positron48/robot/ai-renders/00023-1572373519.png

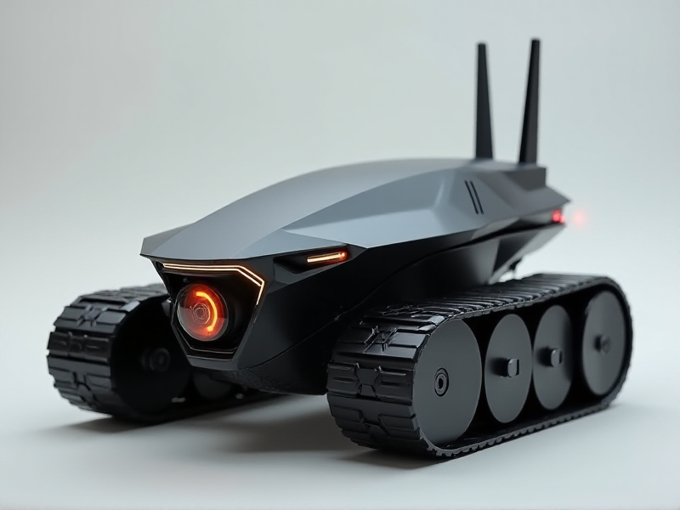
ai-renders/00023-1572373519.png
