positron48/robot/ai-renders/00040-1572373536.png

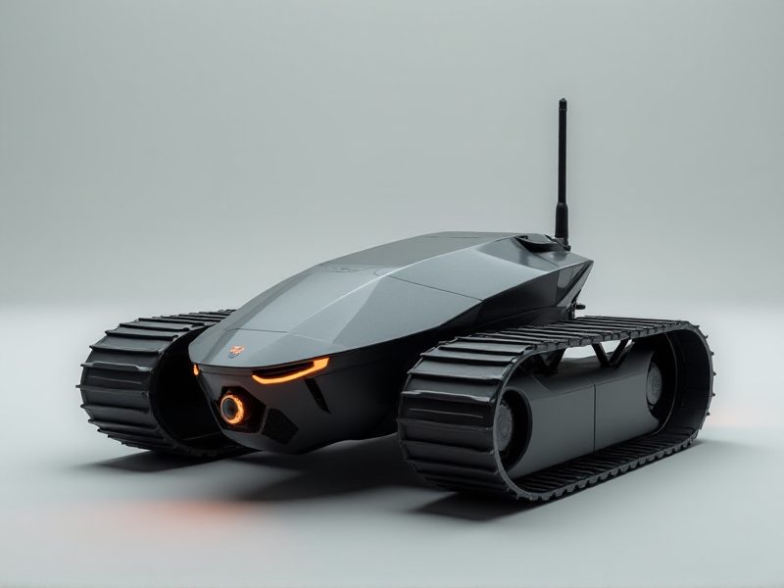
ai-renders/00040-1572373536.png
