positron48/robot/ai-renders/00042-1572373538.png

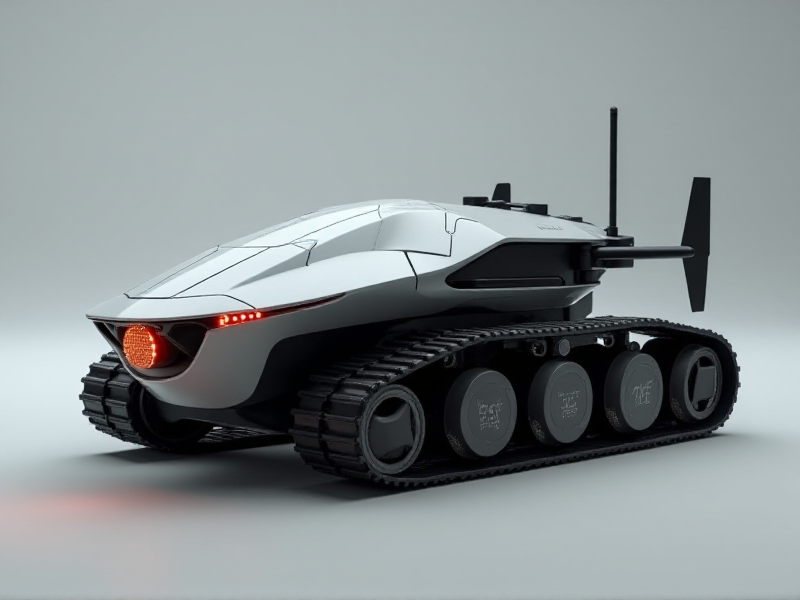
ai-renders/00042-1572373538.png
