positron48/robot/ai-renders/00055-1572373551.png

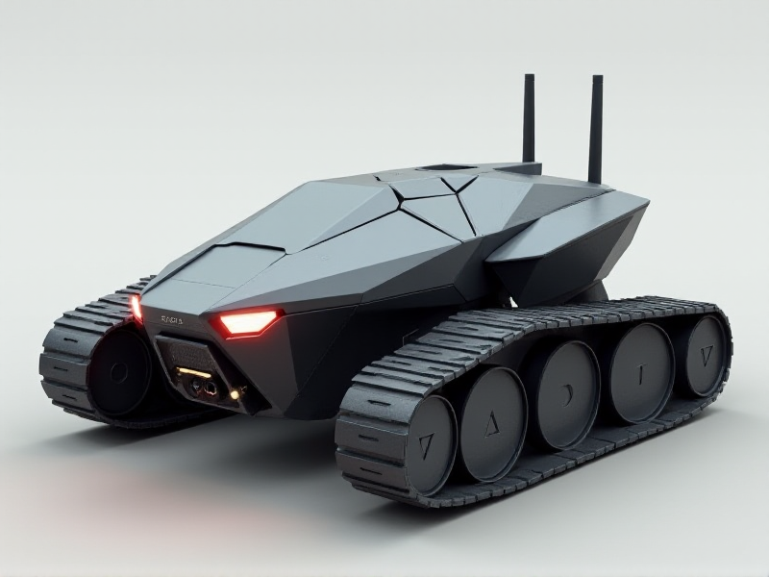
ai-renders/00055-1572373551.png
