positron48/robot/ai-renders/00080-1572373576.png

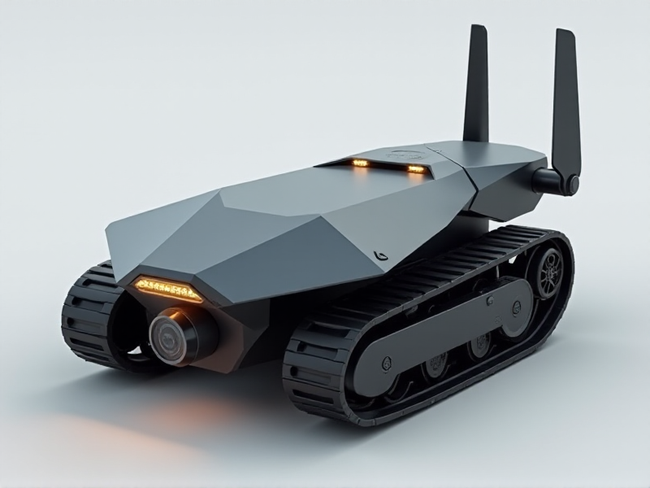
ai-renders/00080-1572373576.png
