positron48/robot/ai-renders/00095-1572373591.png

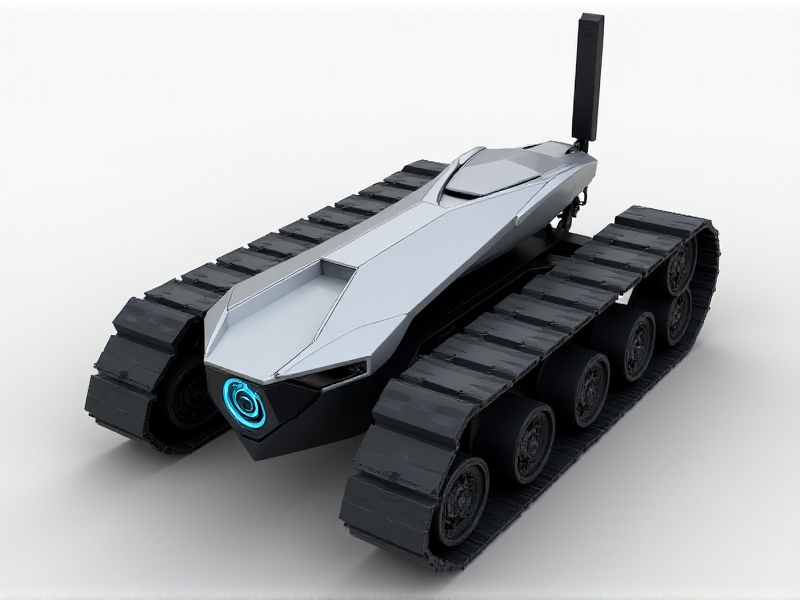
ai-renders/00095-1572373591.png
