positron48/robot/ai-renders/00117-2419401898.png

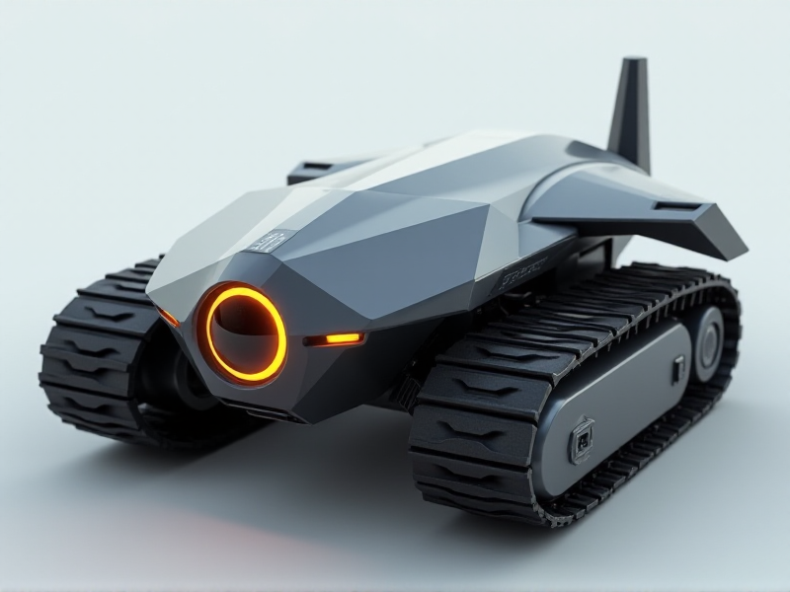
ai-renders/00117-2419401898.png
