positron48/robot/ai-renders/00122-3091978869.png

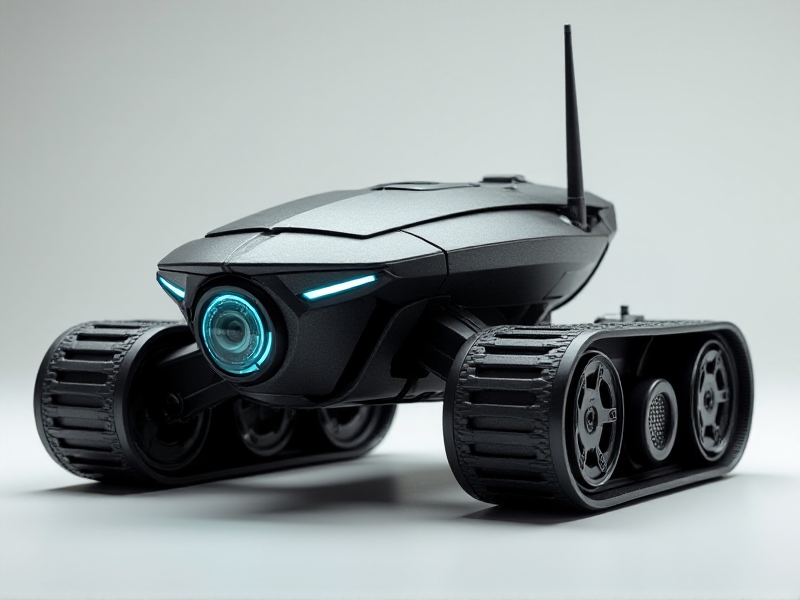
ai-renders/00122-3091978869.png
