positron48/robot/ai-renders/00186-2854738076.png

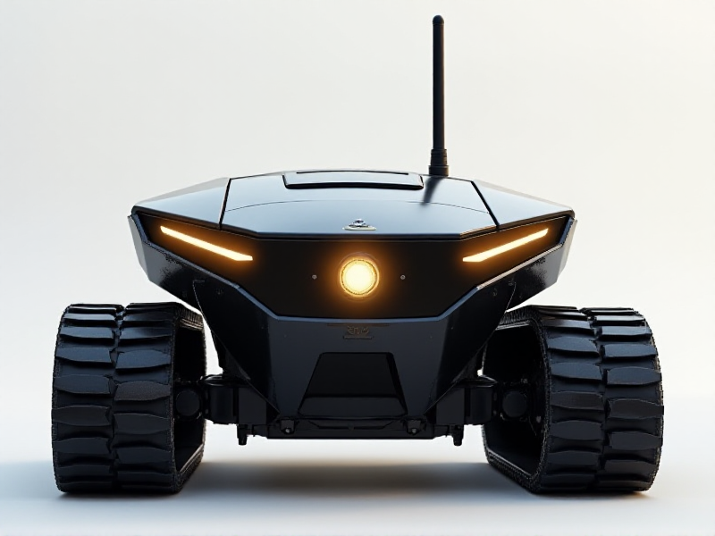
ai-renders/00186-2854738076.png
