positron48/robot/ai-renders/00576-1258968118.png

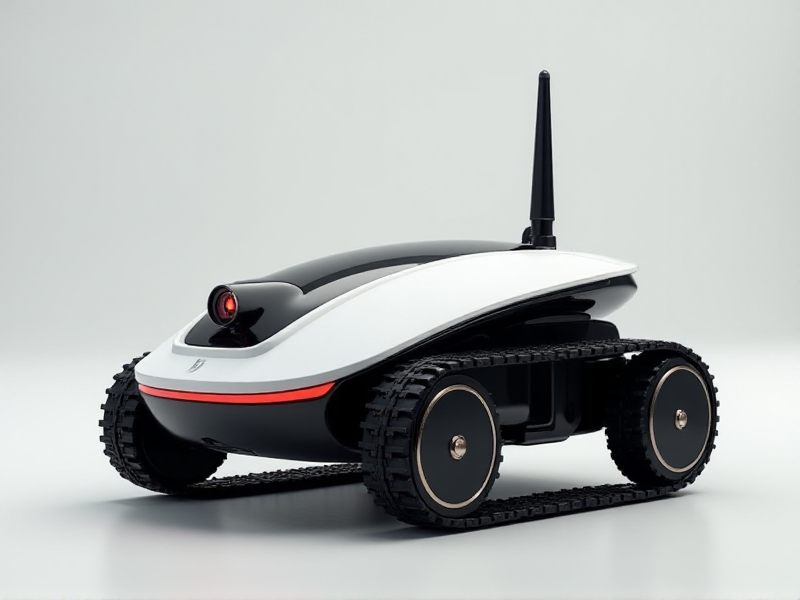
ai-renders/00576-1258968118.png
