positron48/robot/ai-renders/all/00000-357559412.png

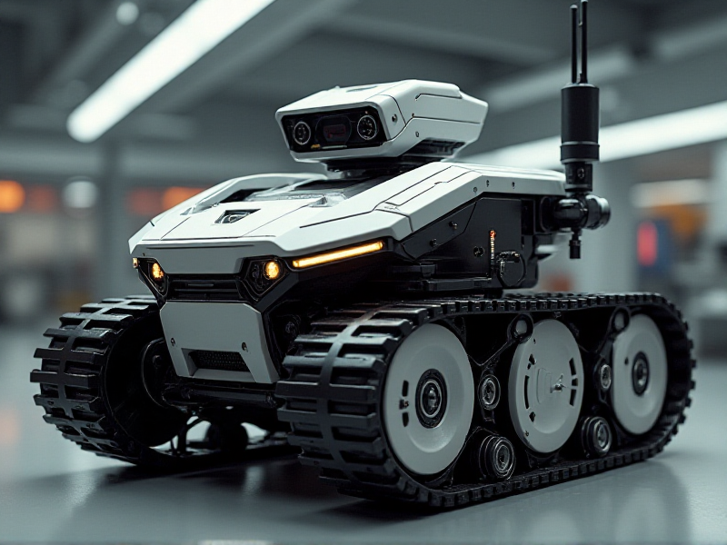
ai-renders/all/00000-357559412.png
