positron48/robot/ai-renders/all/00005-1248517951.png

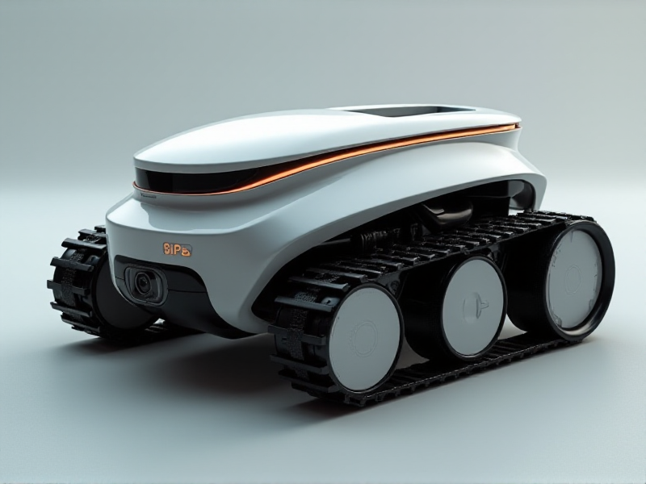
ai-renders/all/00005-1248517951.png
