positron48/robot/ai-renders/all/00009-1846332725.png

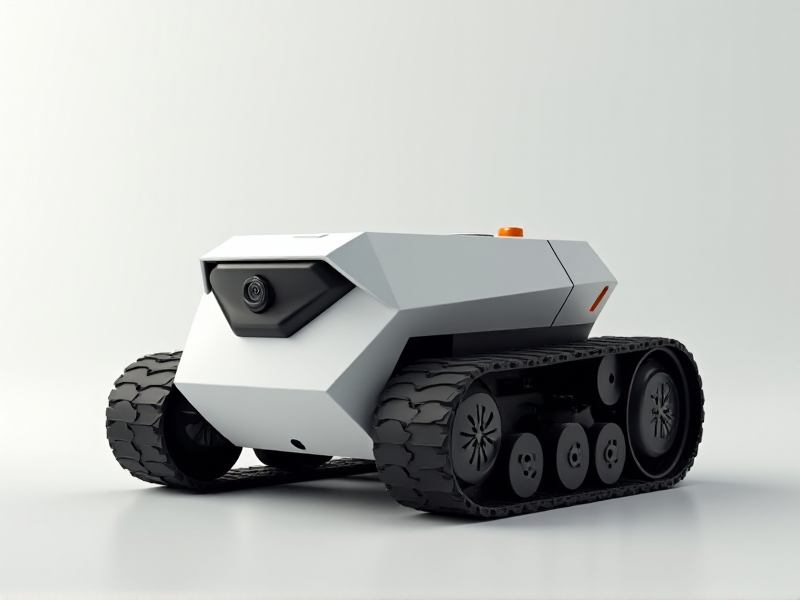
ai-renders/all/00009-1846332725.png
