positron48/robot/ai-renders/all/00010-3830520620.png

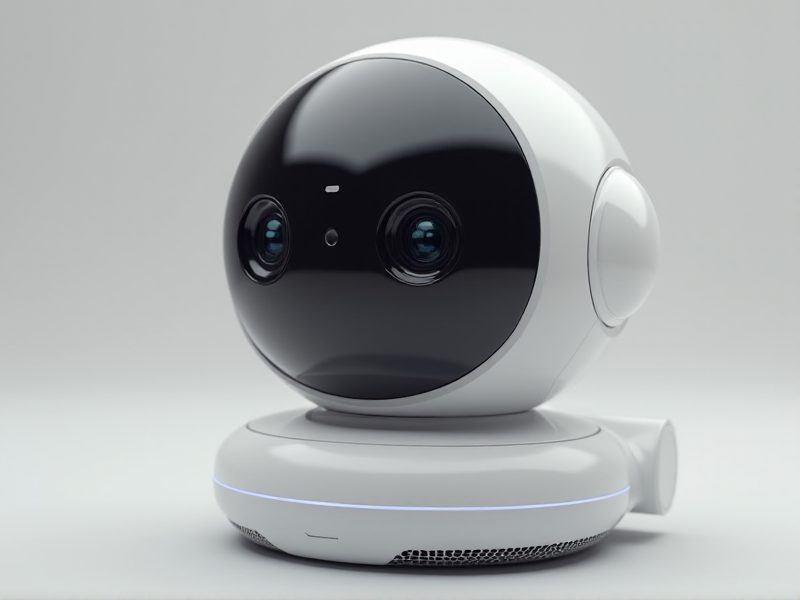
ai-renders/all/00010-3830520620.png
