positron48/robot/ai-renders/all/00015-1510084404.png

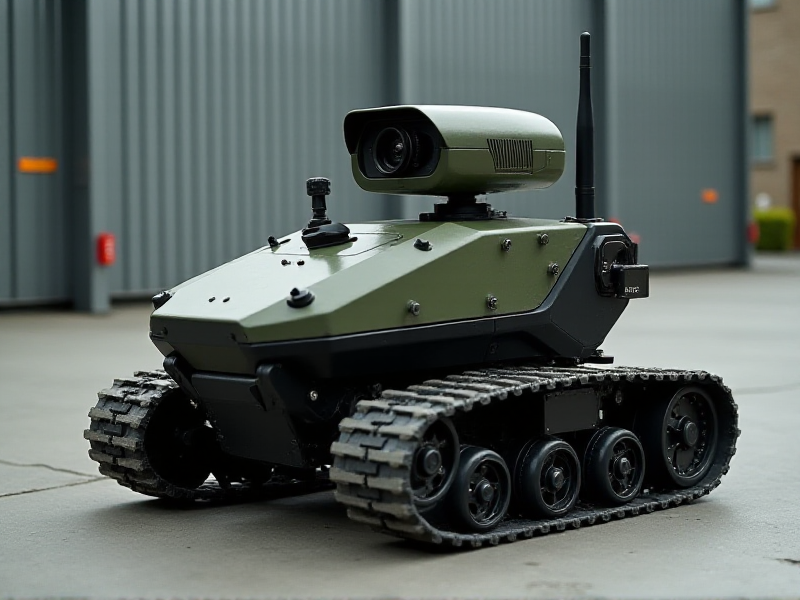
ai-renders/all/00015-1510084404.png
