positron48/robot/ai-renders/all/00020-1703099426.png

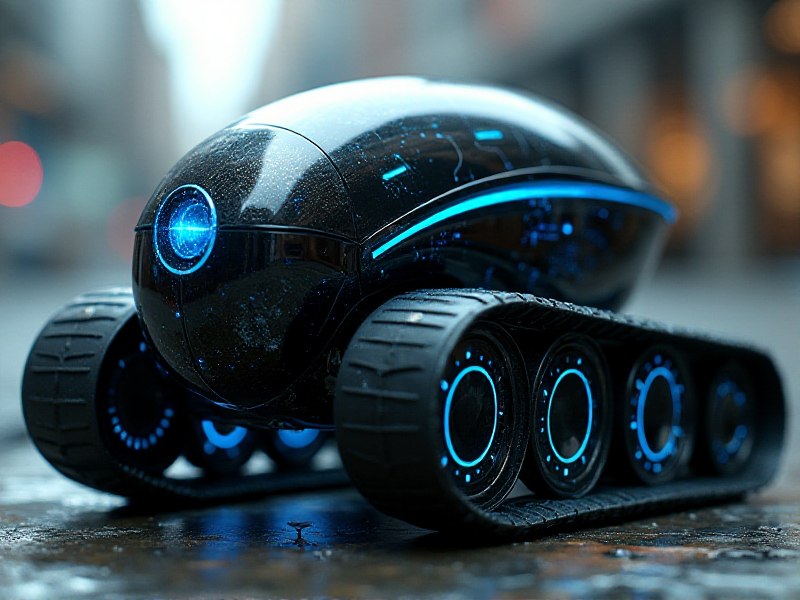
ai-renders/all/00020-1703099426.png
