positron48/robot/ai-renders/all/00024-1435315715.png

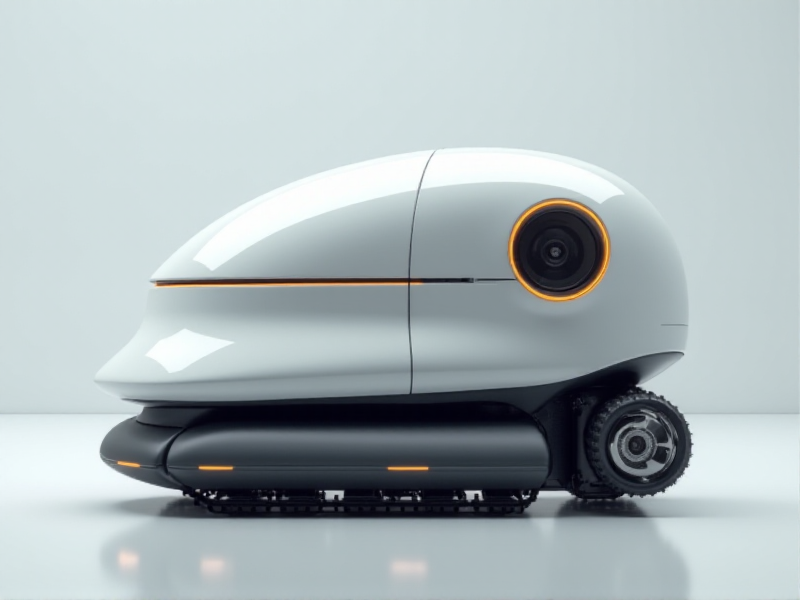
ai-renders/all/00024-1435315715.png
