positron48/robot/ai-renders/all/00025-1704890410.png

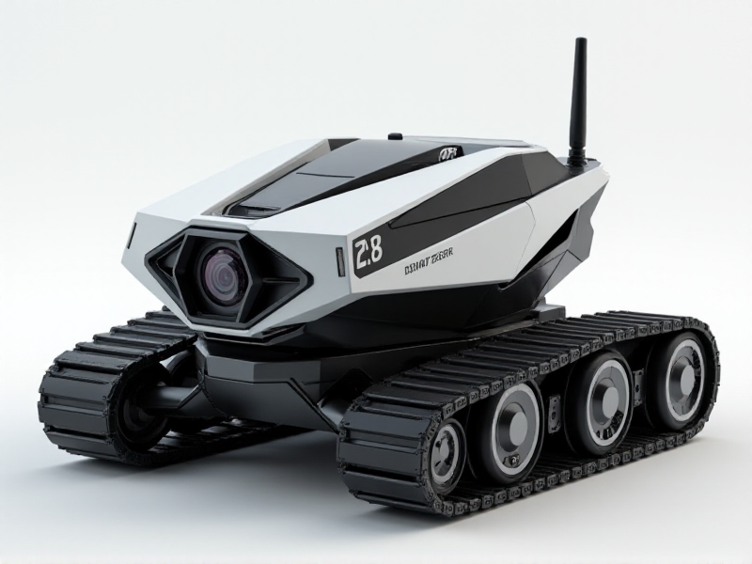
ai-renders/all/00025-1704890410.png
