positron48/robot/ai-renders/all/00030-3104922929.png

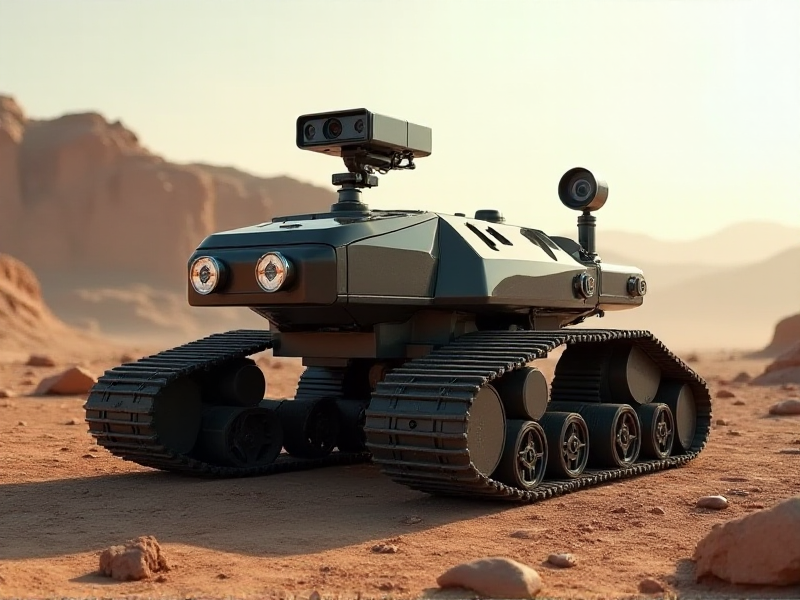
ai-renders/all/00030-3104922929.png
