positron48/robot/ai-renders/all/00035-3908900121.png

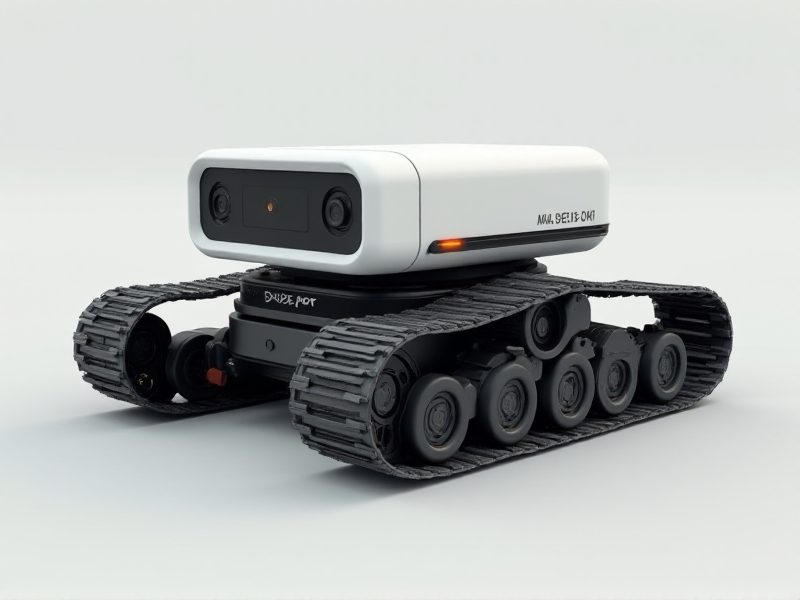
ai-renders/all/00035-3908900121.png
