positron48/robot/ai-renders/all/00039-2805063001.png

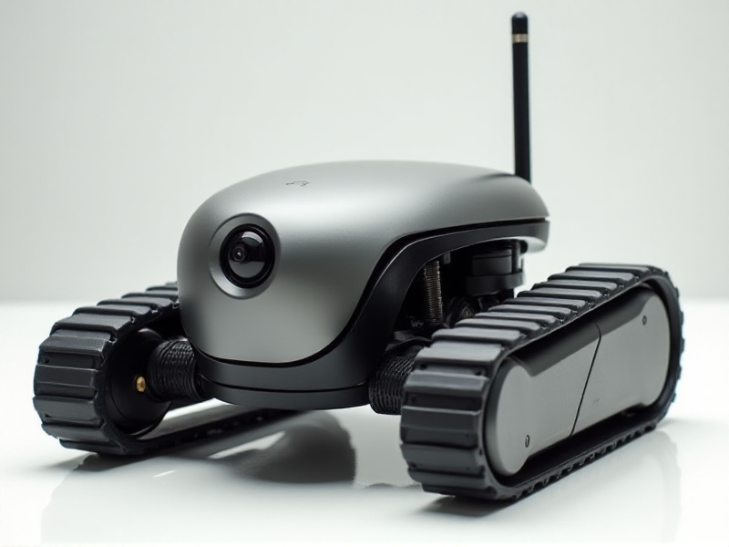
ai-renders/all/00039-2805063001.png
