positron48/robot/ai-renders/all/00040-1279062750.png

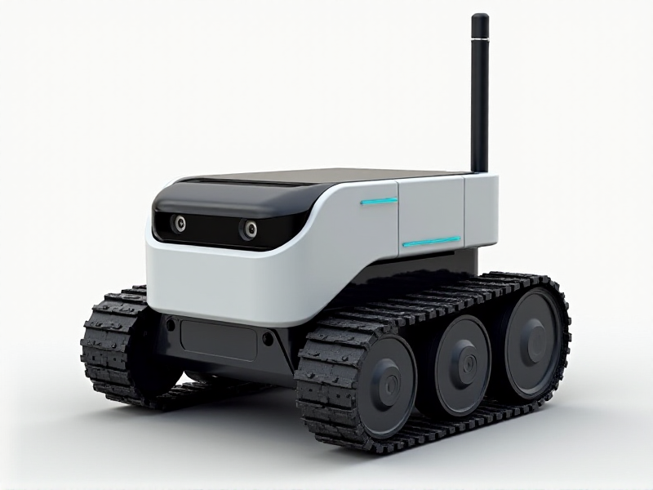
ai-renders/all/00040-1279062750.png
