positron48/robot/ai-renders/all/00045-1480606769.png

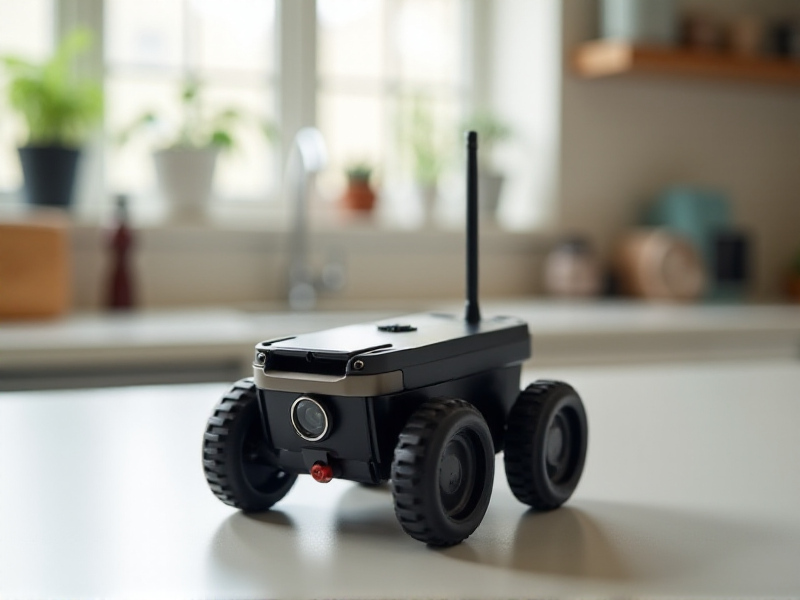
ai-renders/all/00045-1480606769.png
