positron48/robot/ai-renders/all/00050-4032314944.png

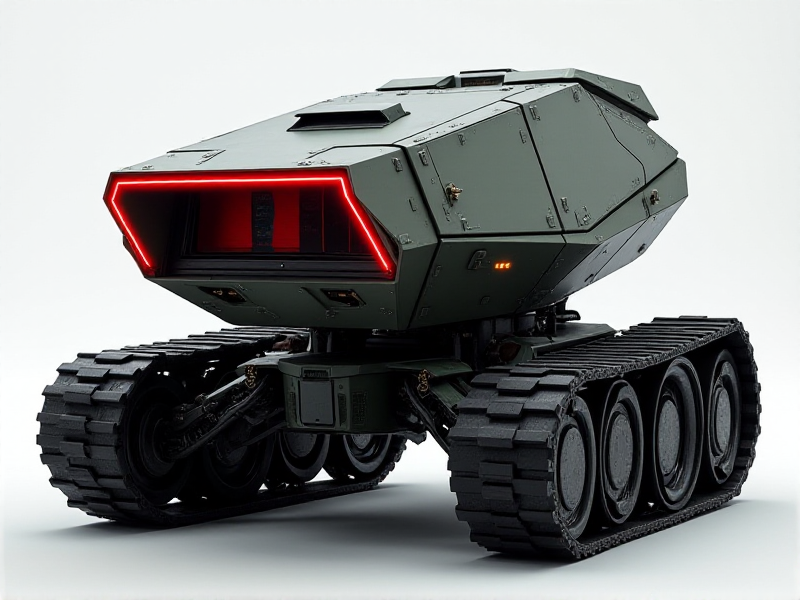
ai-renders/all/00050-4032314944.png
