positron48/robot/ai-renders/all/00054-1610239201.png

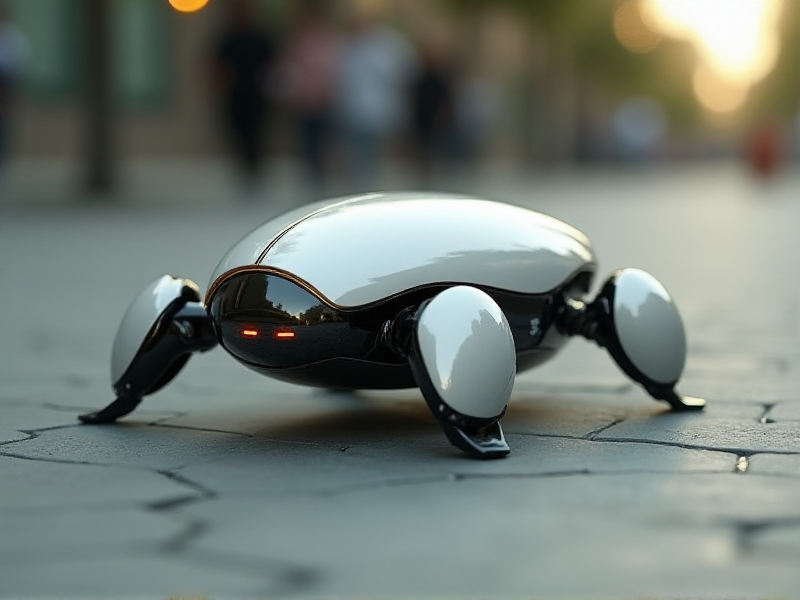
ai-renders/all/00054-1610239201.png
