positron48/robot/ai-renders/all/00055-1120741218.png

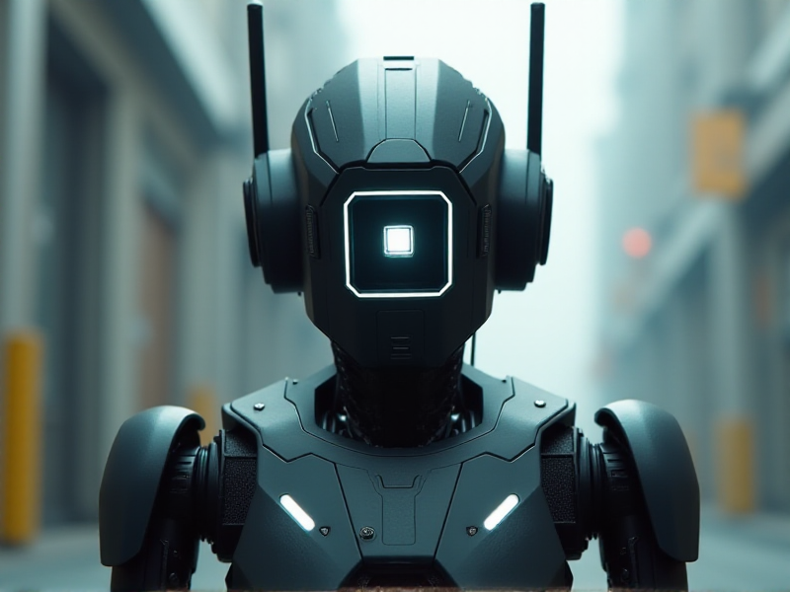
ai-renders/all/00055-1120741218.png
