positron48/robot/ai-renders/all/00060-2551709868.png

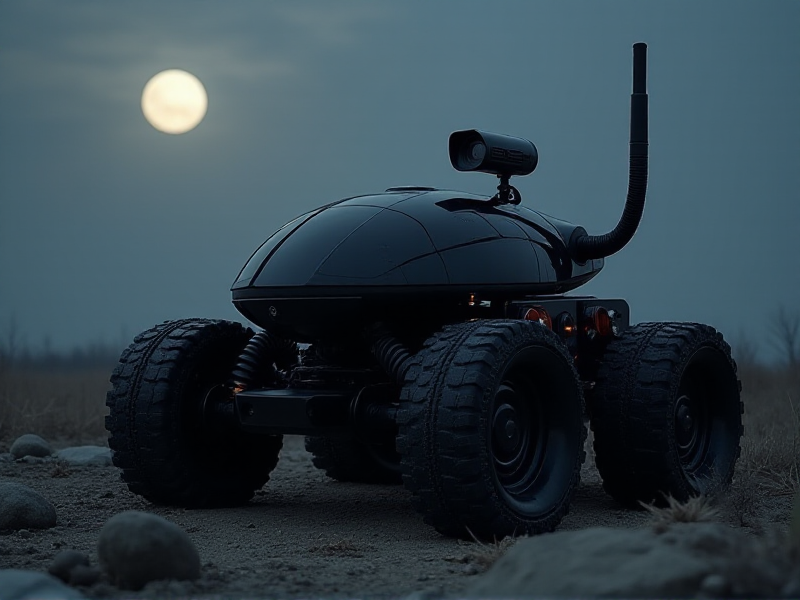
ai-renders/all/00060-2551709868.png
