positron48/robot/ai-renders/all/00065-3160654962.png

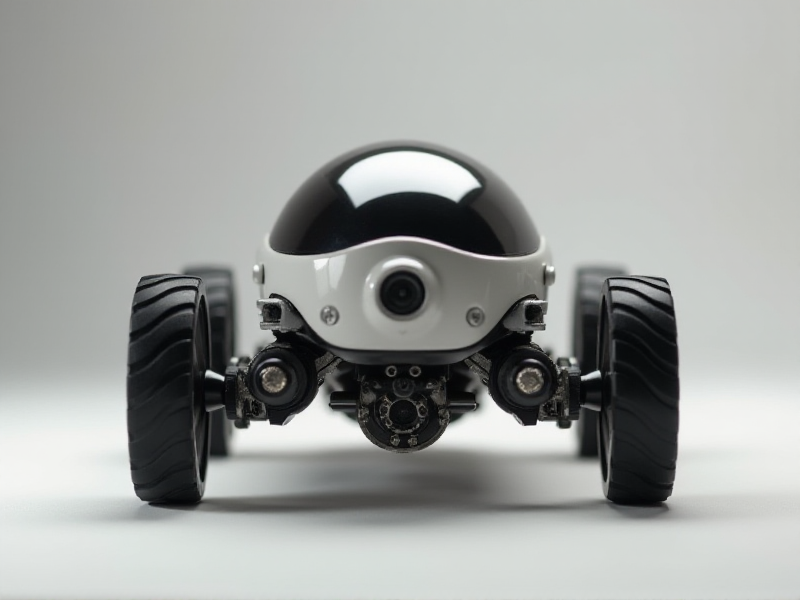
ai-renders/all/00065-3160654962.png
