positron48/robot/ai-renders/all/00069-1434522783.png

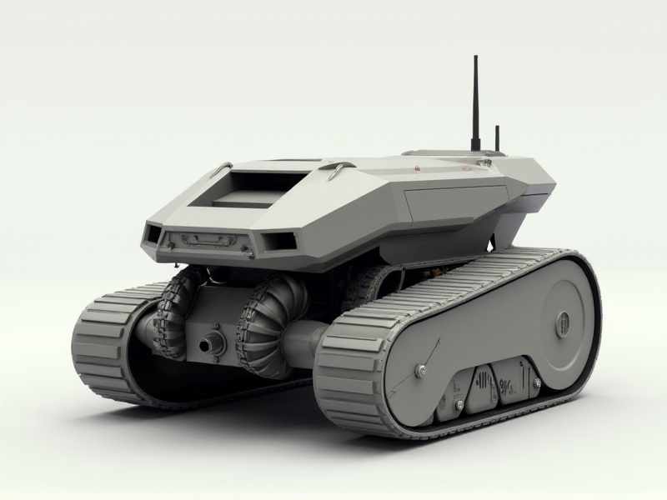
ai-renders/all/00069-1434522783.png
