positron48/robot/ai-renders/all/00070-909880307.png

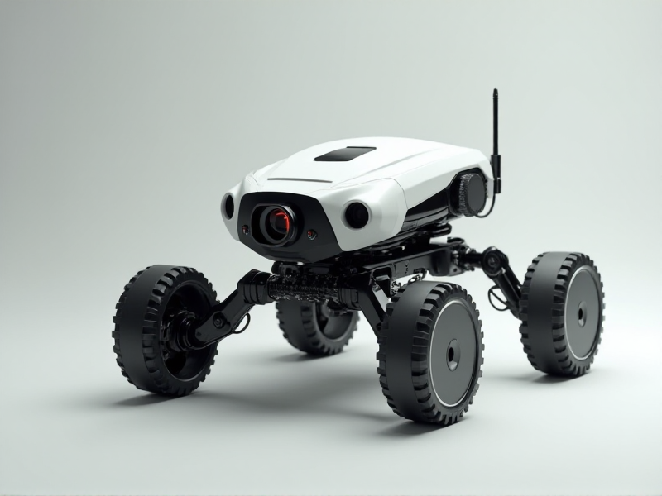
ai-renders/all/00070-909880307.png
