positron48/robot/ai-renders/all/00075-4185142455.png

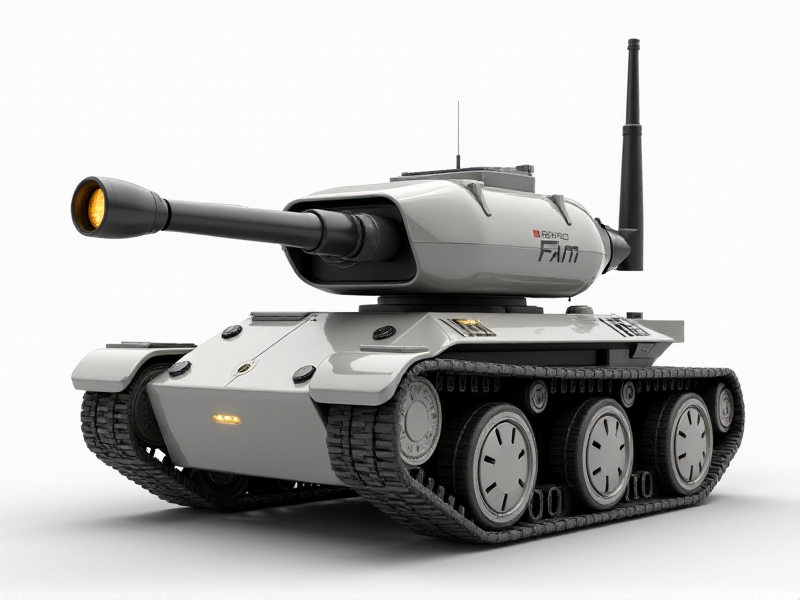
ai-renders/all/00075-4185142455.png
