positron48/robot/ai-renders/all/00080-3249783718.png

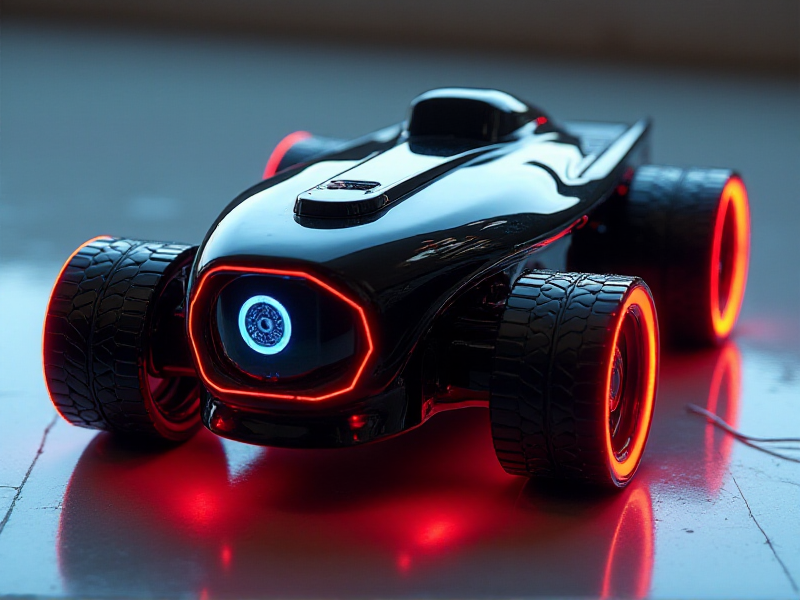
ai-renders/all/00080-3249783718.png
