positron48/robot/ai-renders/all/00085-1067350489.png

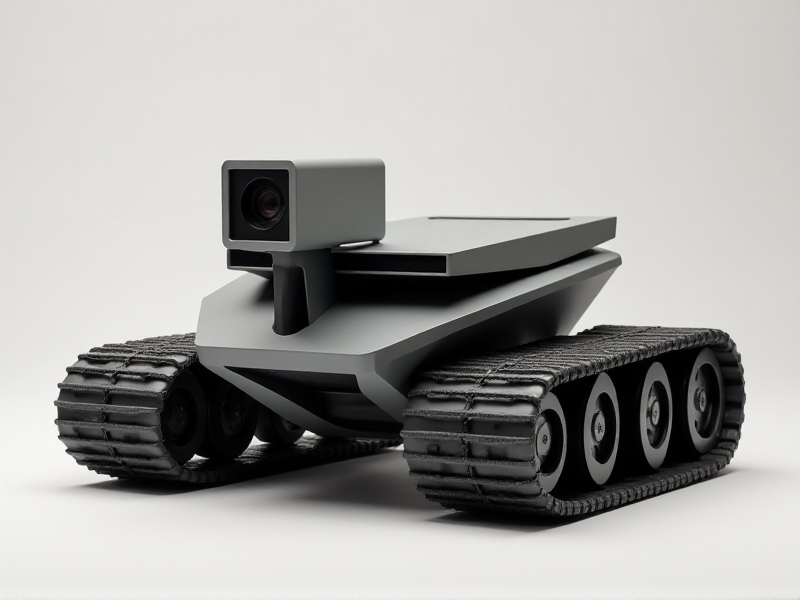
ai-renders/all/00085-1067350489.png
