positron48/robot/ai-renders/all/00090-1672998109.png

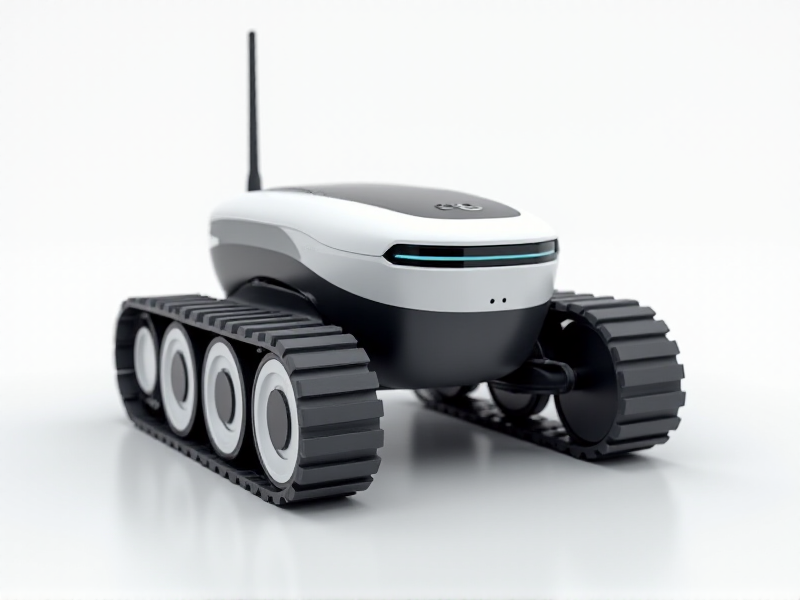
ai-renders/all/00090-1672998109.png
