positron48/robot/ai-renders/all/00095-99025422.png

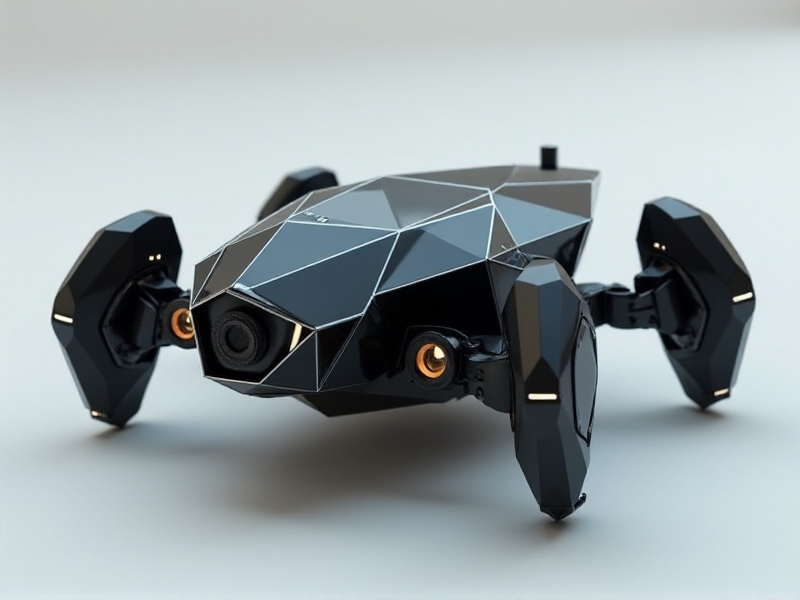
ai-renders/all/00095-99025422.png
