positron48/robot/ai-renders/all/00100-3047387080.png

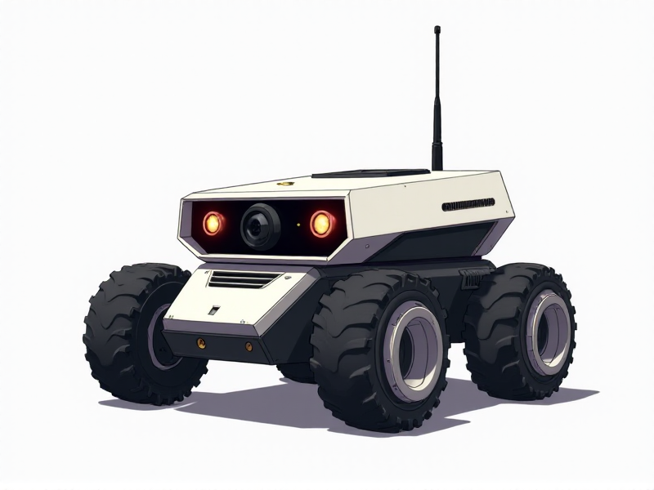
ai-renders/all/00100-3047387080.png
