positron48/robot/ai-renders/all/00105-2527510471.png

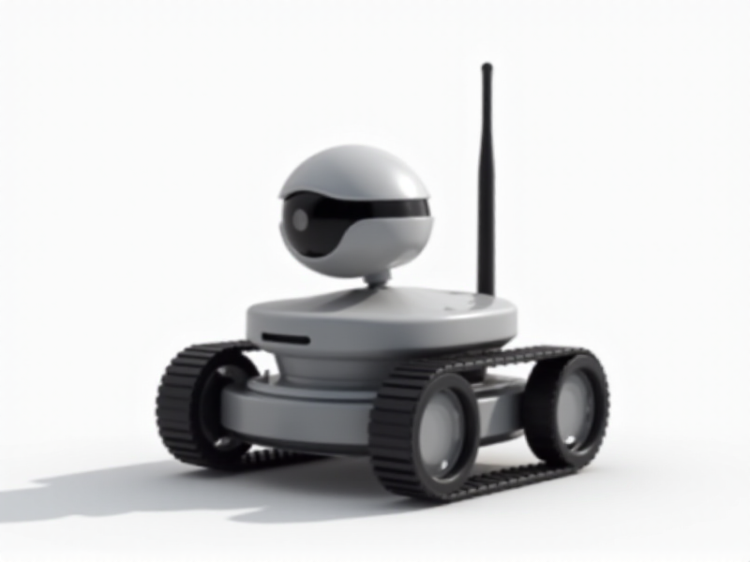
ai-renders/all/00105-2527510471.png
