positron48/robot/ai-renders/all/00110-1504034849.png

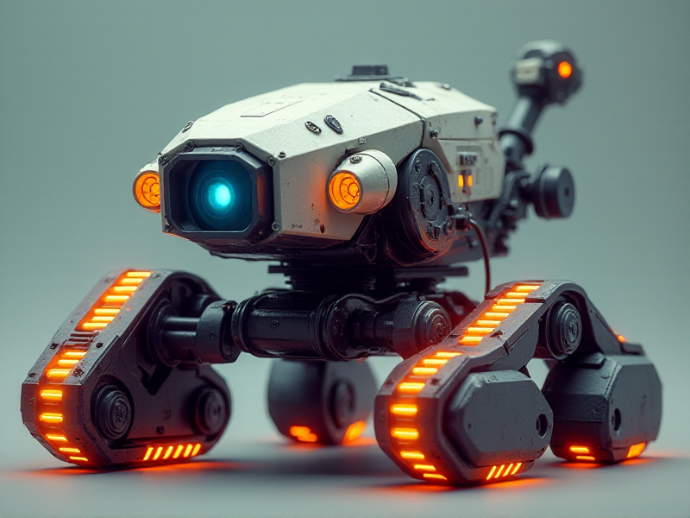
ai-renders/all/00110-1504034849.png
