positron48/robot/ai-renders/all/00115-2866515047.png

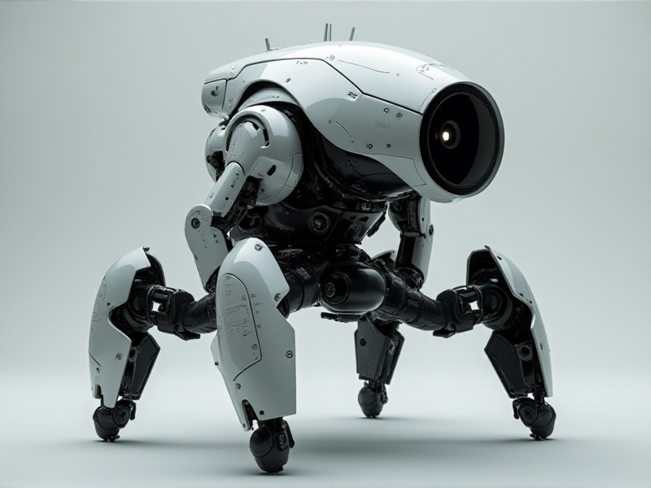
ai-renders/all/00115-2866515047.png
