positron48/robot/ai-renders/all/00120-1237886460.png

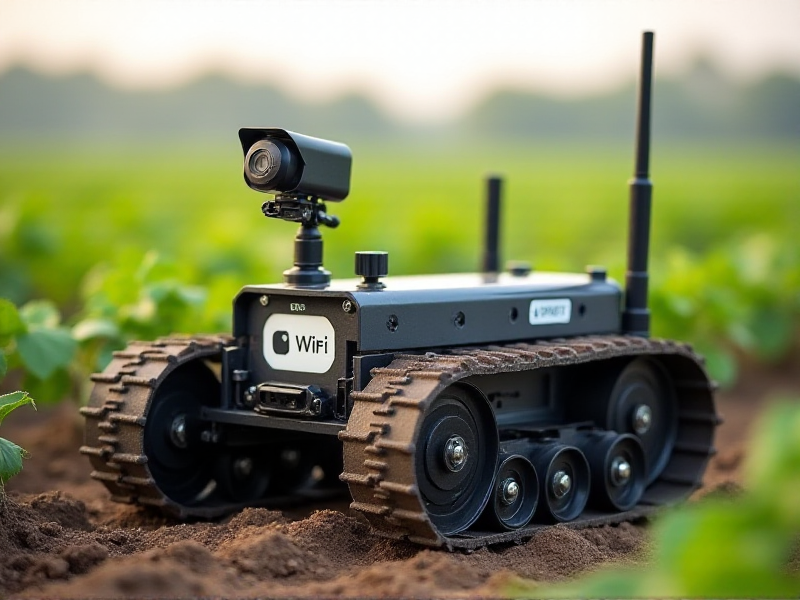
ai-renders/all/00120-1237886460.png
