positron48/robot/ai-renders/all/00125-3579262042.png

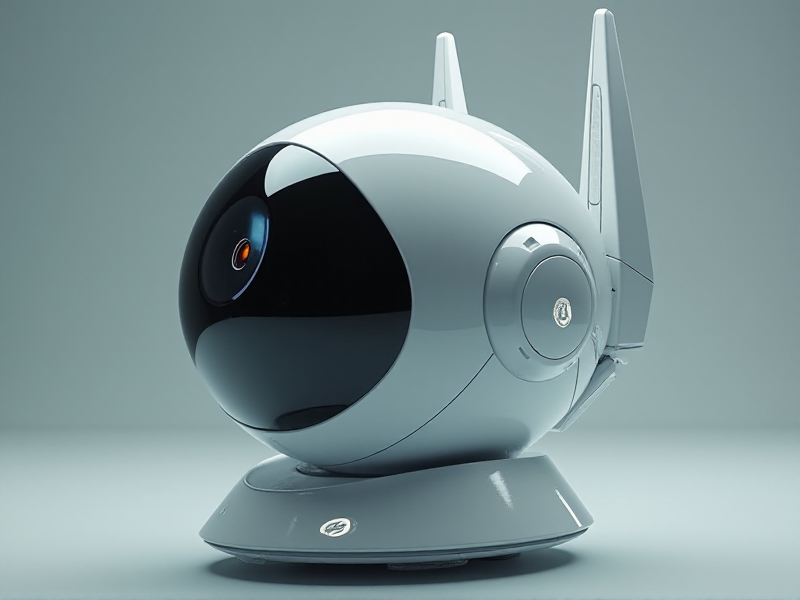
ai-renders/all/00125-3579262042.png
