positron48/robot/ai-renders/all/00130-2607103277.png

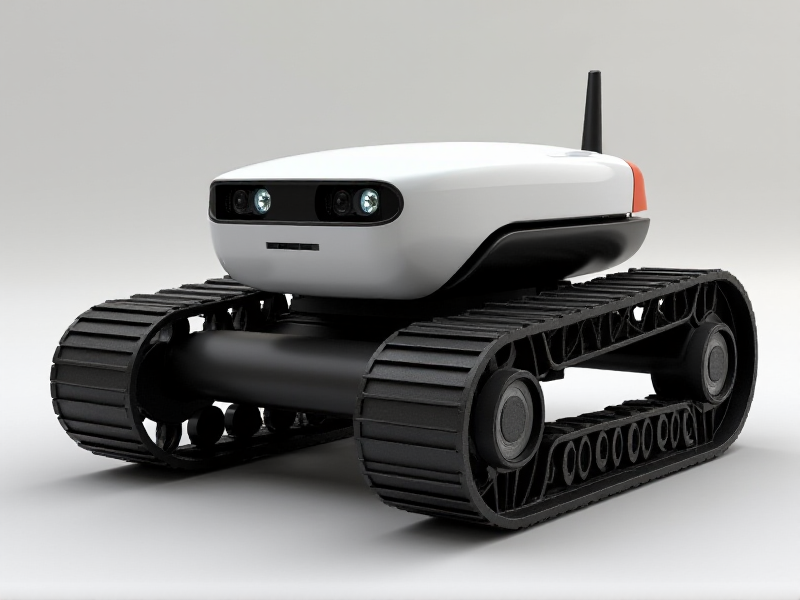
ai-renders/all/00130-2607103277.png
