positron48/robot/ai-renders/all/00135-3617314966.png

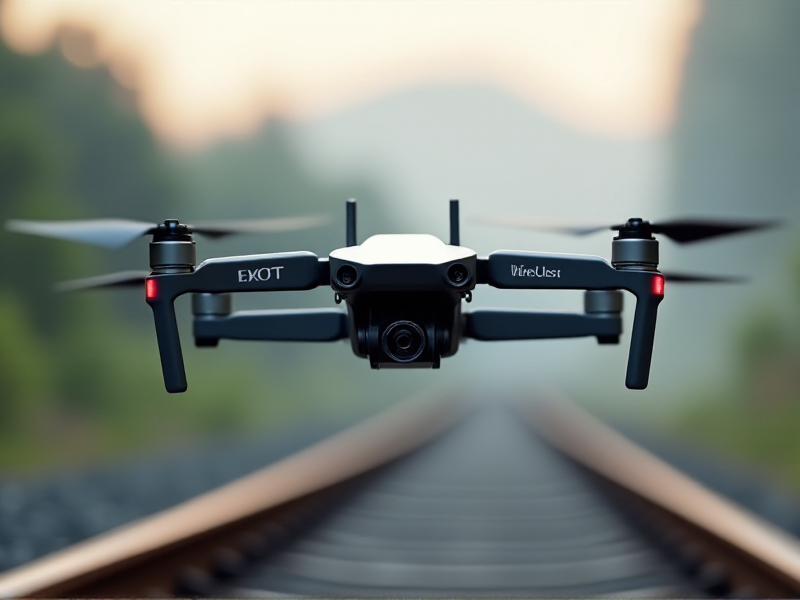
ai-renders/all/00135-3617314966.png
