positron48/robot/ai-renders/all/00140-2341996741.png

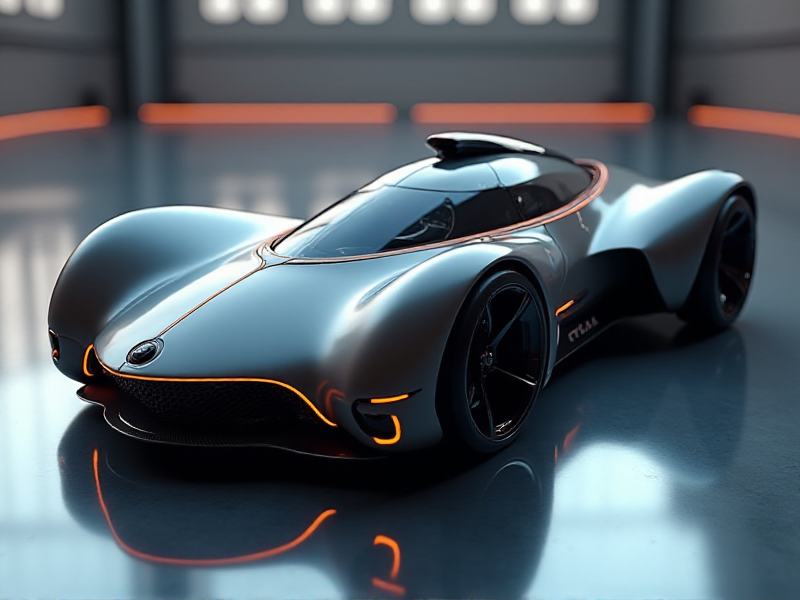
ai-renders/all/00140-2341996741.png
