positron48/robot/ai-renders/all/00145-1462839352.png

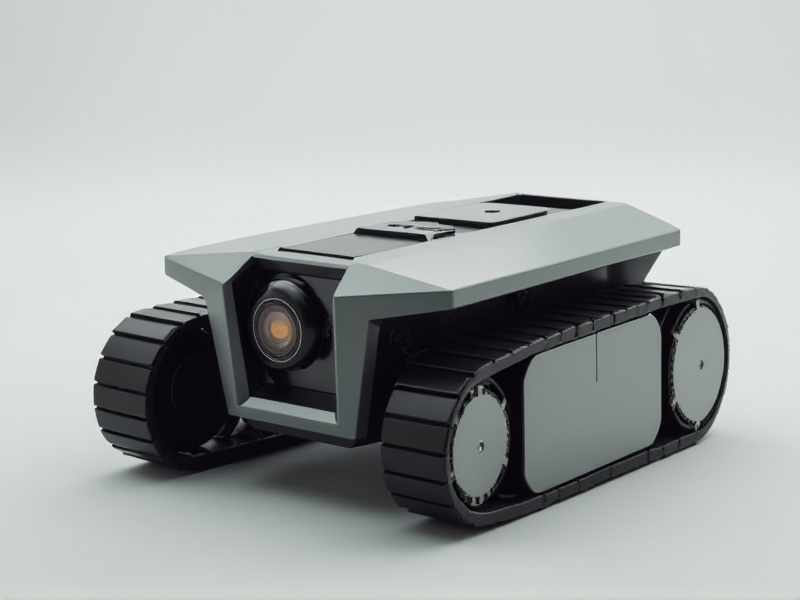
ai-renders/all/00145-1462839352.png
