positron48/robot/ai-renders/all/00150-565781888.png

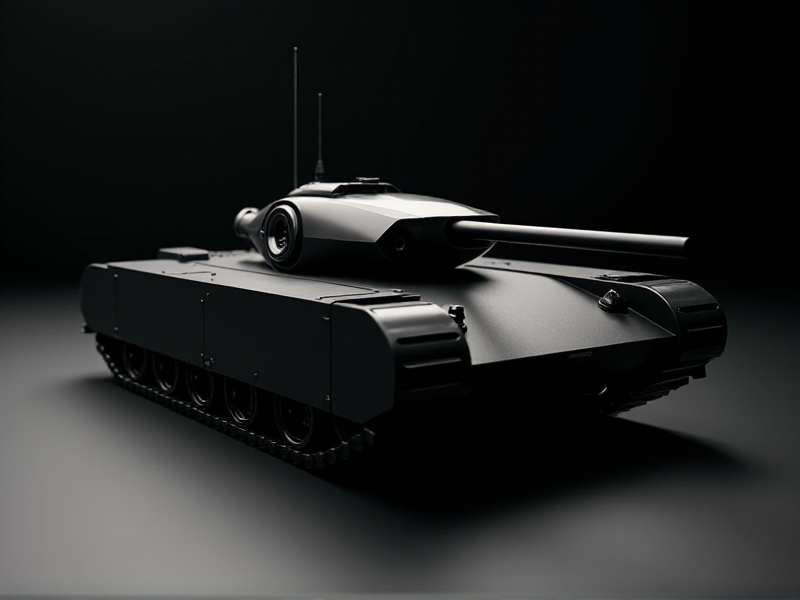
ai-renders/all/00150-565781888.png
