positron48/robot/ai-renders/all/00155-3509653221.png

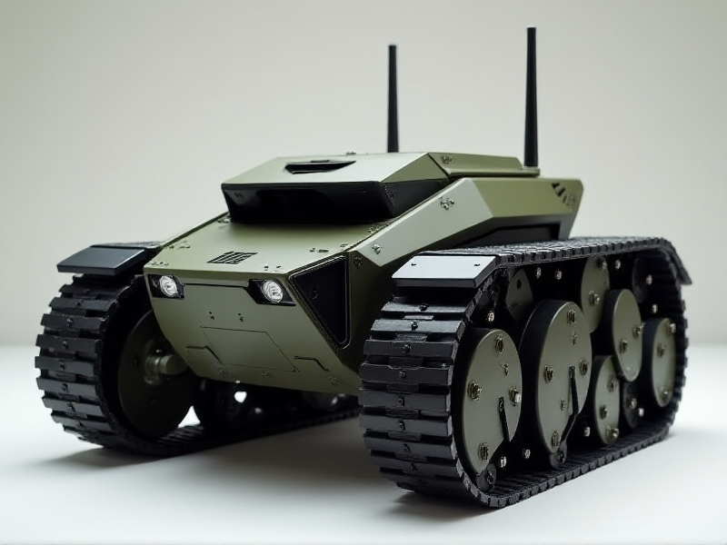
ai-renders/all/00155-3509653221.png
