positron48/robot/ai-renders/all/00160-556067007.png

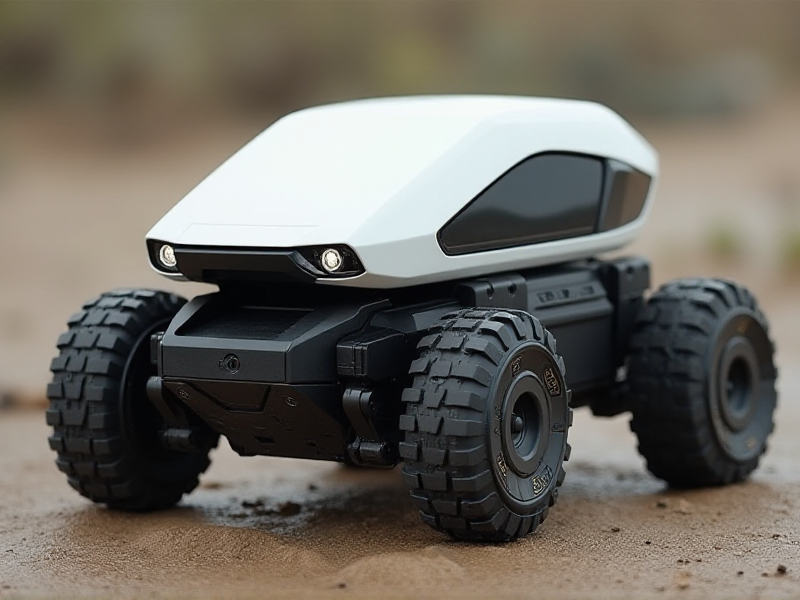
ai-renders/all/00160-556067007.png
