positron48/robot/ai-renders/all/00165-1893324952.png

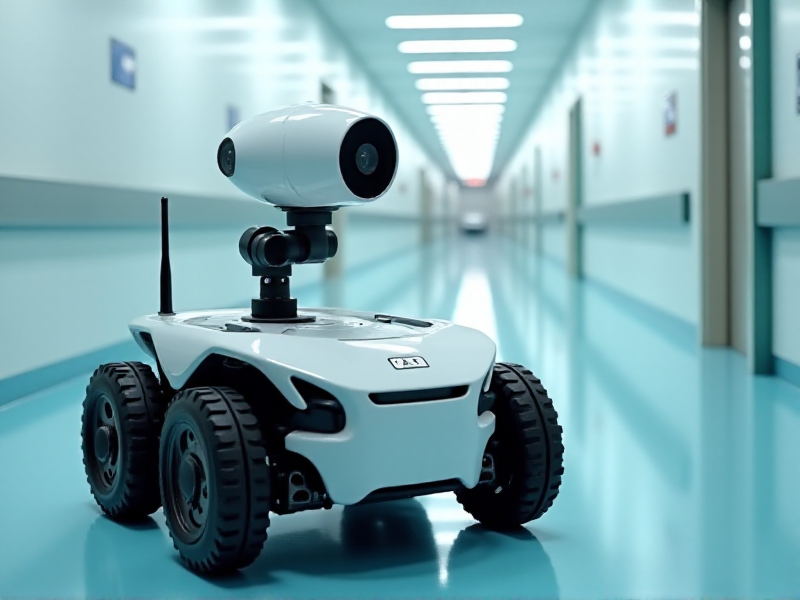
ai-renders/all/00165-1893324952.png
