positron48/robot/ai-renders/all/00170-3917874720.png

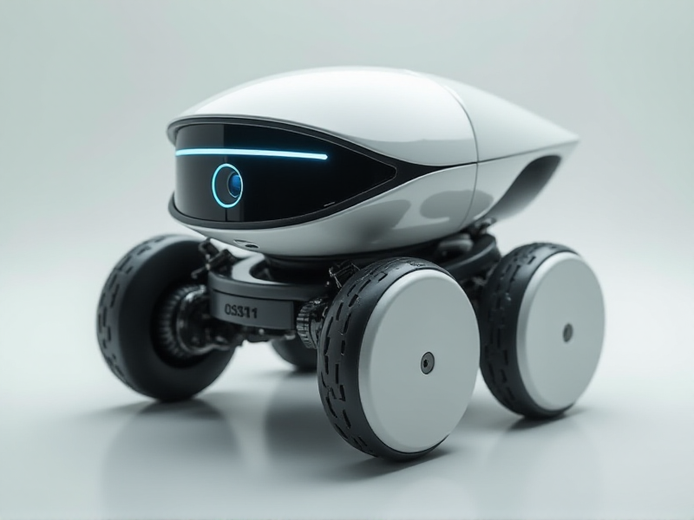
ai-renders/all/00170-3917874720.png
