positron48/robot/ai-renders/all/00175-3374178357.png

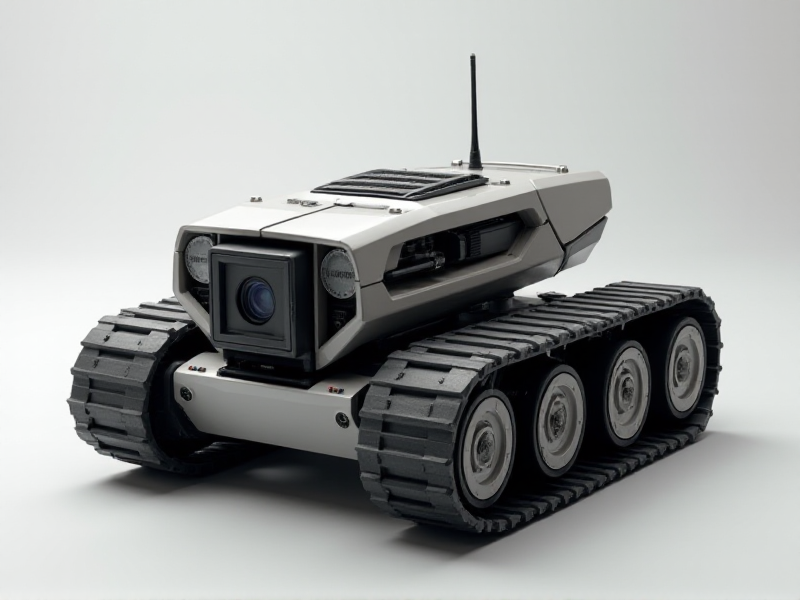
ai-renders/all/00175-3374178357.png
