positron48/robot/ai-renders/all/00180-371988289.png

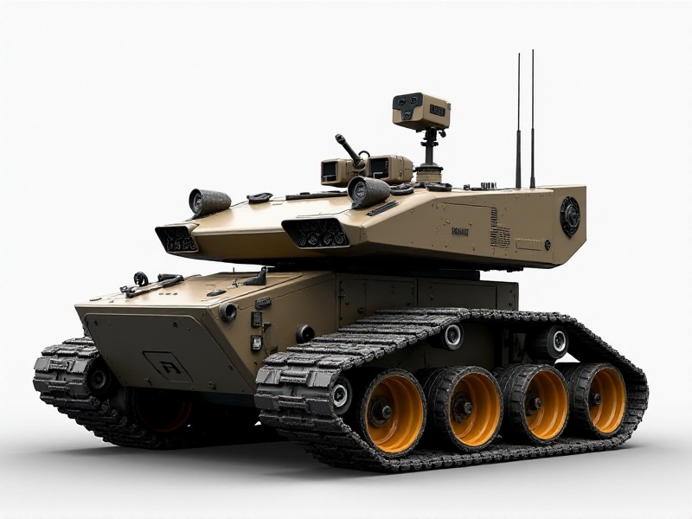
ai-renders/all/00180-371988289.png
