positron48/robot/ai-renders/all/00185-975864008.png

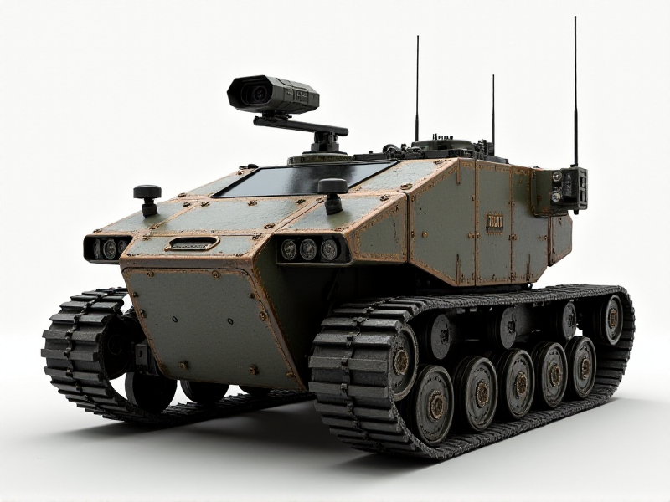
ai-renders/all/00185-975864008.png
