positron48/robot/ai-renders/all/00190-273683321.png

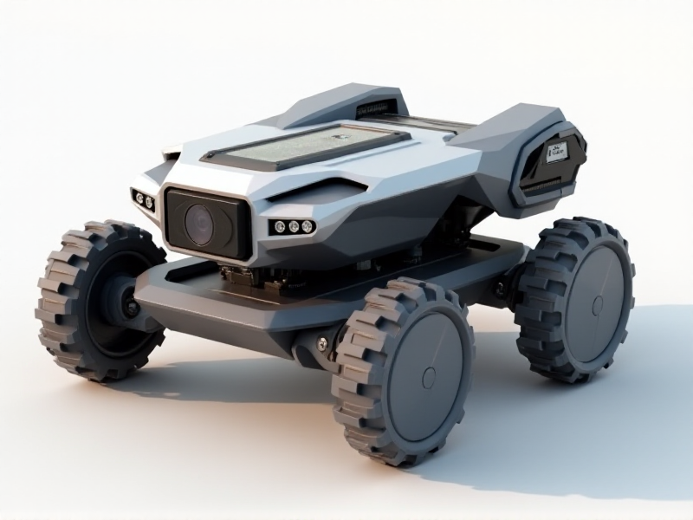
ai-renders/all/00190-273683321.png
