positron48/robot/ai-renders/all/00195-471412829.png

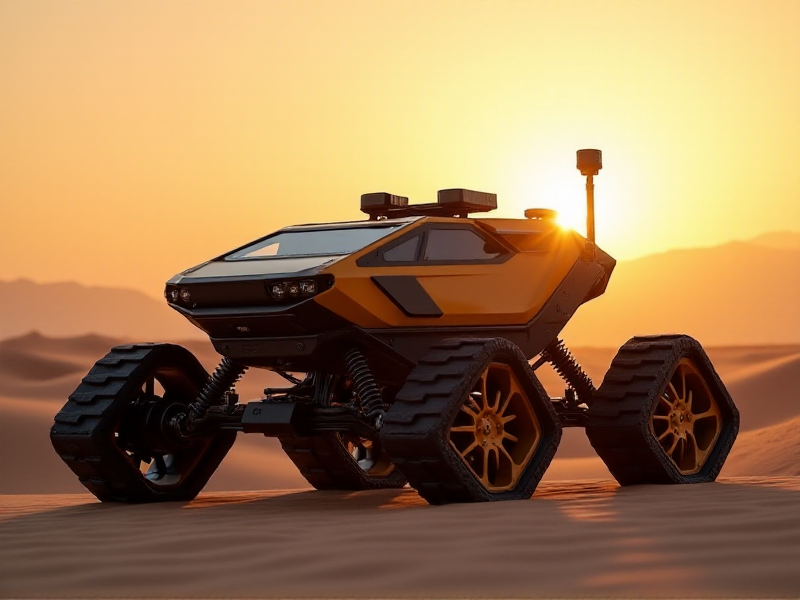
ai-renders/all/00195-471412829.png
