positron48/robot/ai-renders/all/00200-3361338232.png

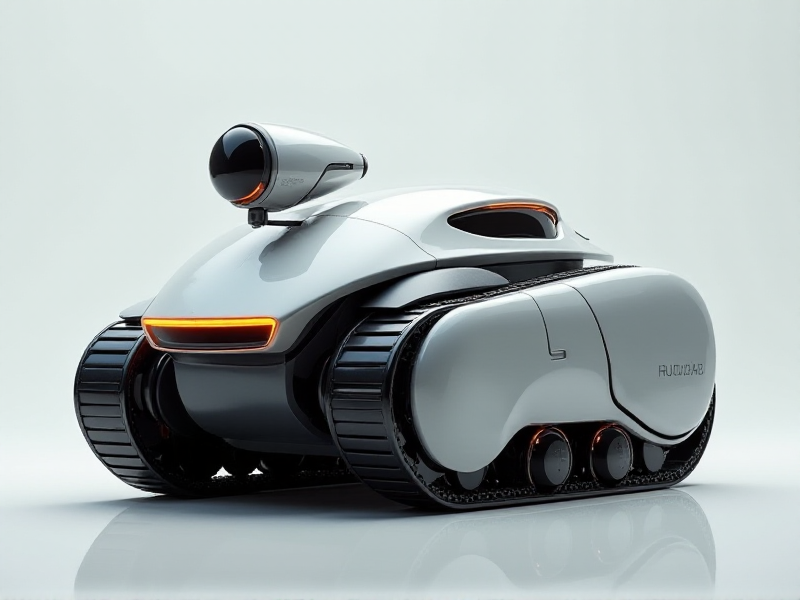
ai-renders/all/00200-3361338232.png
