positron48/robot/ai-renders/all/00205-2477551414.png

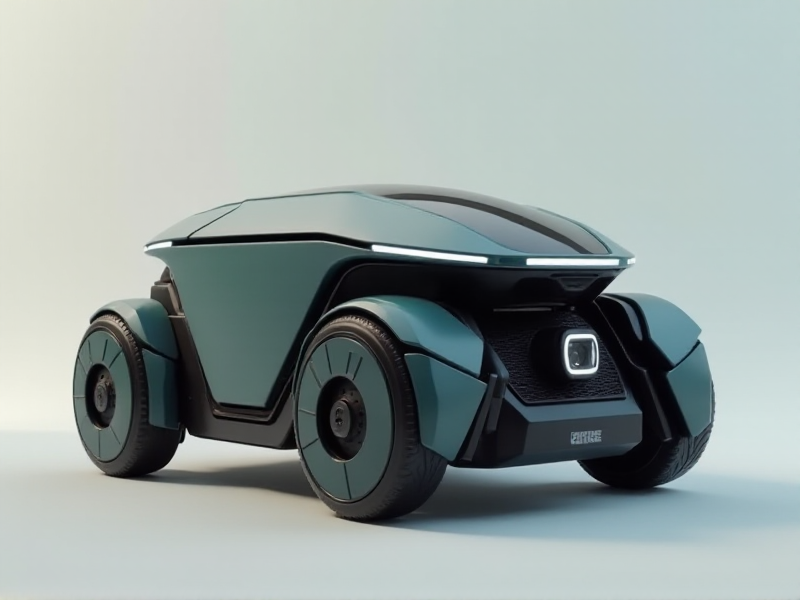
ai-renders/all/00205-2477551414.png
