positron48/robot/ai-renders/all/00210-2080022012.png

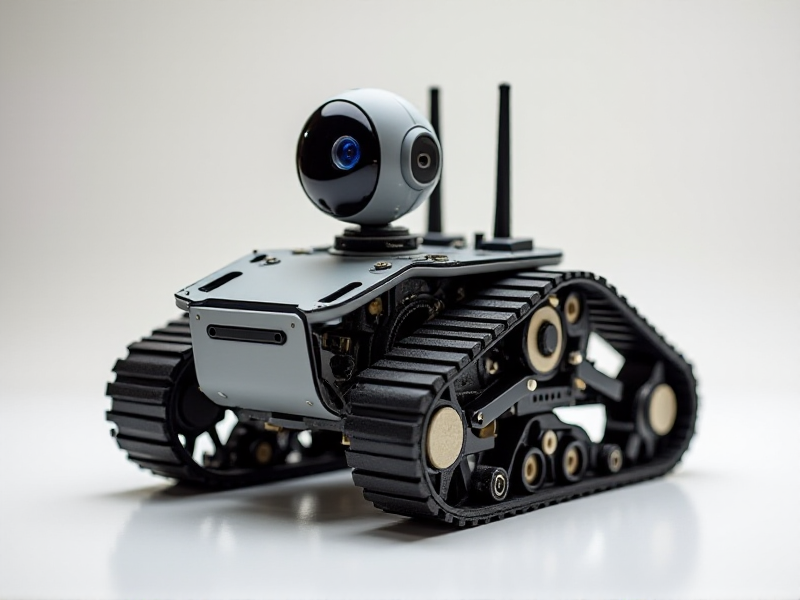
ai-renders/all/00210-2080022012.png
