positron48/robot/ai-renders/all/00215-3676958083.png

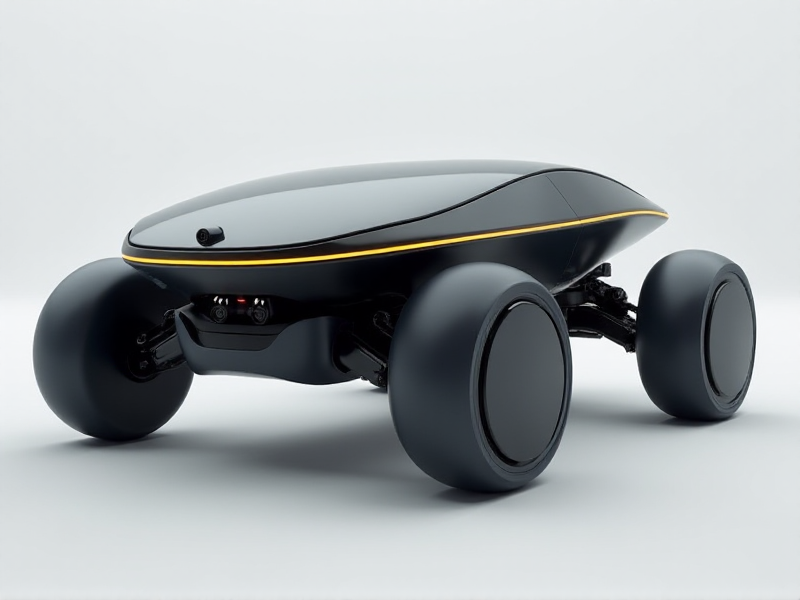
ai-renders/all/00215-3676958083.png
