positron48/robot/ai-renders/all/00220-1926256563.png

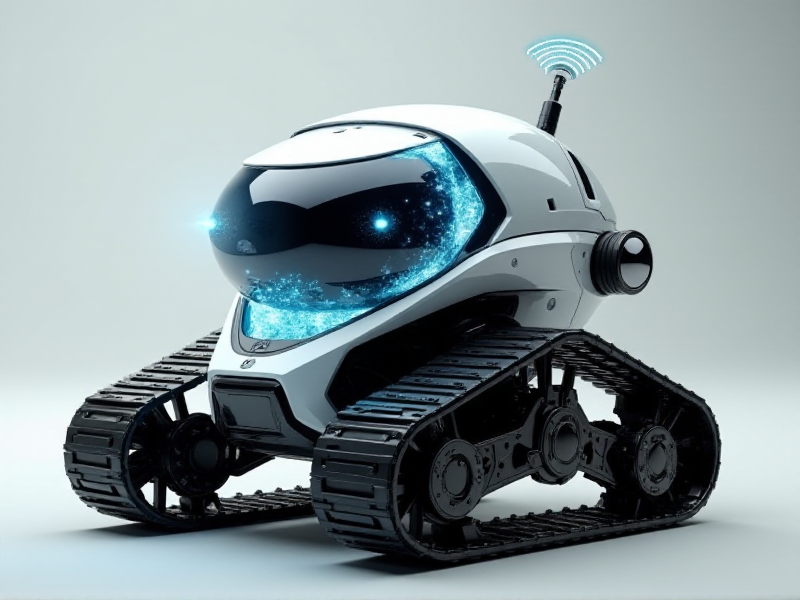
ai-renders/all/00220-1926256563.png
