positron48/robot/ai-renders/all/00225-3037877225.png

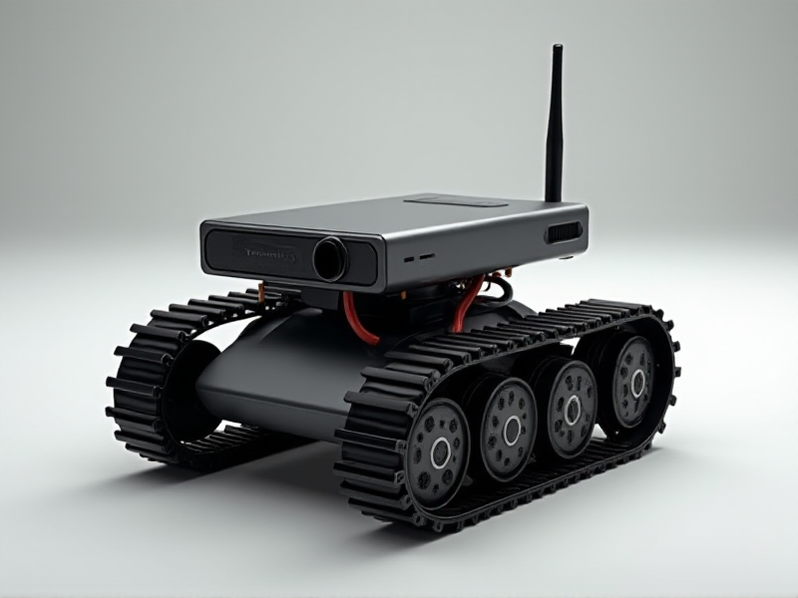
ai-renders/all/00225-3037877225.png
