positron48/robot/ai-renders/all/00230-1827474017.png

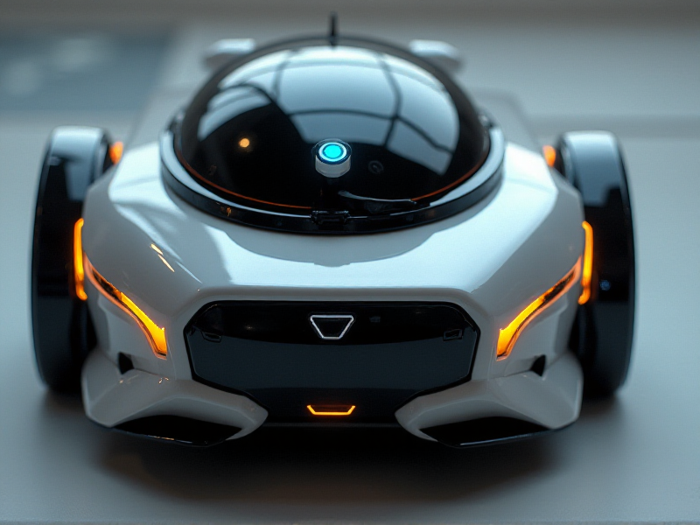
ai-renders/all/00230-1827474017.png
