positron48/robot/ai-renders/all/00235-2733124412.png

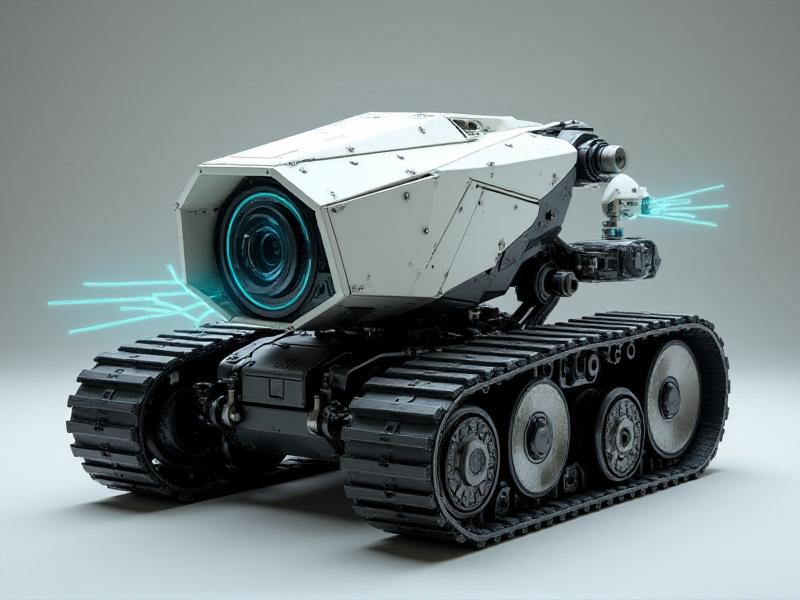
ai-renders/all/00235-2733124412.png
