positron48/robot/ai-renders/all/00240-3910605715.png

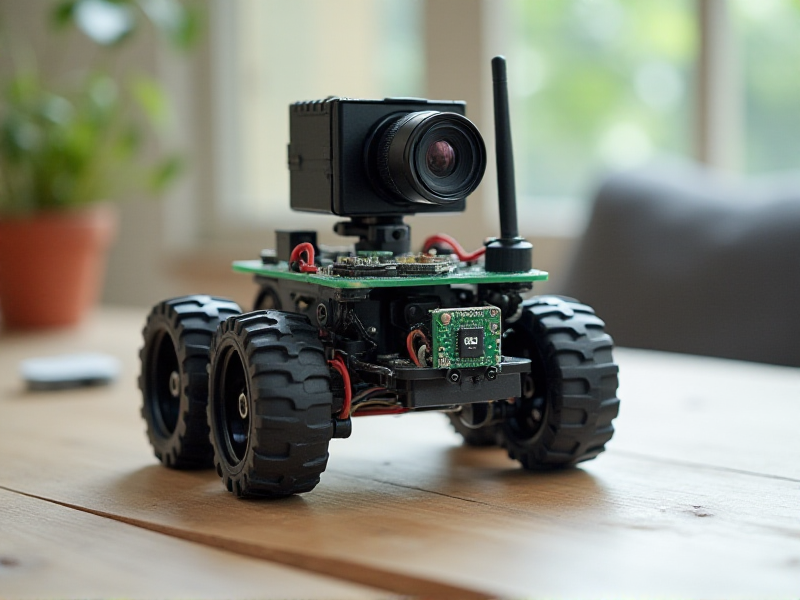
ai-renders/all/00240-3910605715.png
