positron48/robot/ai-renders/all/00245-939561087.png

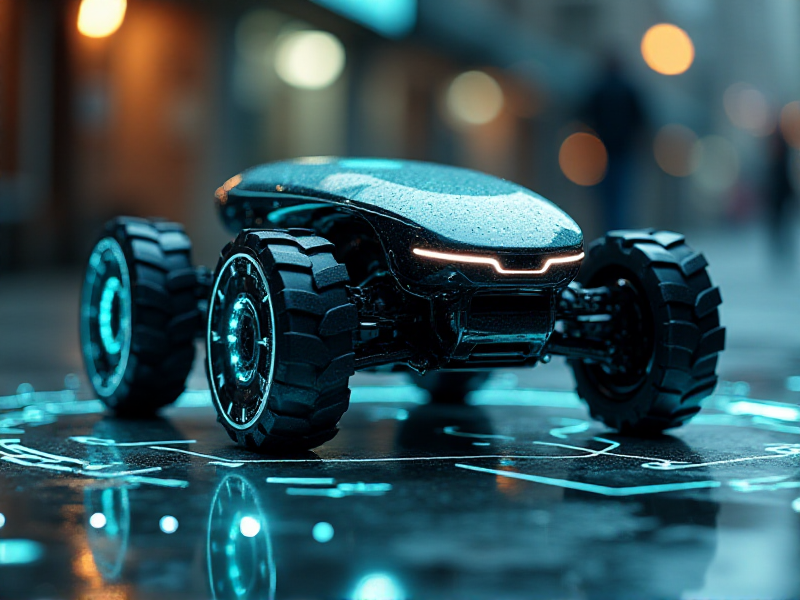
ai-renders/all/00245-939561087.png
