positron48/robot/ai-renders/all/00250-245128935.png

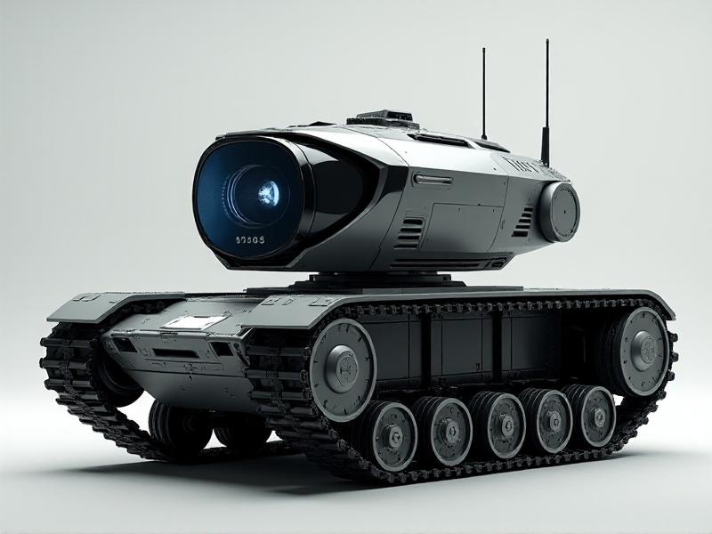
ai-renders/all/00250-245128935.png
