positron48/robot/ai-renders/all/00255-744254574.png

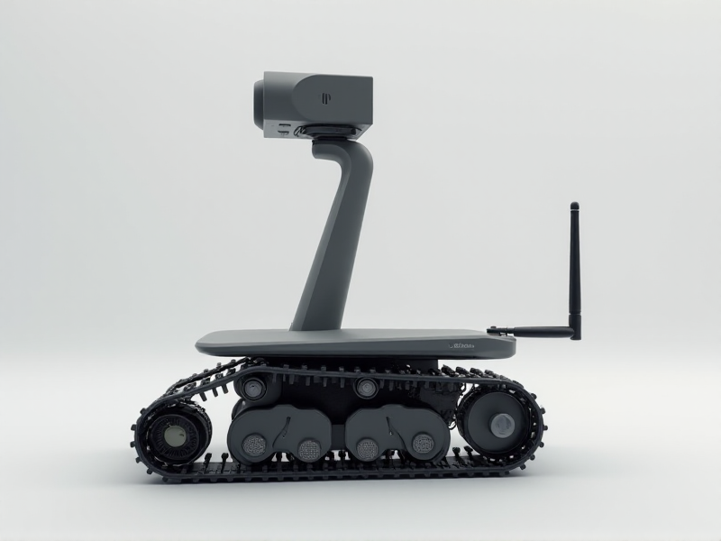
ai-renders/all/00255-744254574.png
