positron48/robot/ai-renders/all/00260-1368395855.png

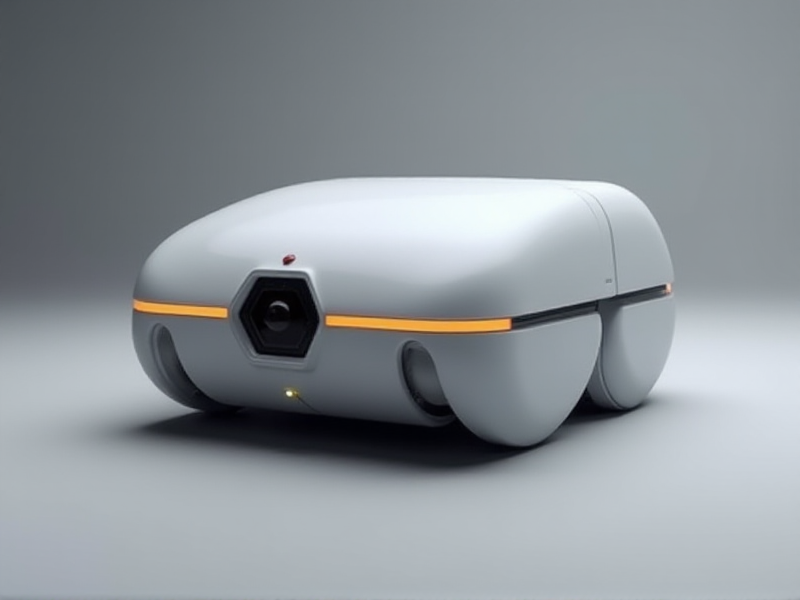
ai-renders/all/00260-1368395855.png
