positron48/robot/ai-renders/all/00265-995517853.png

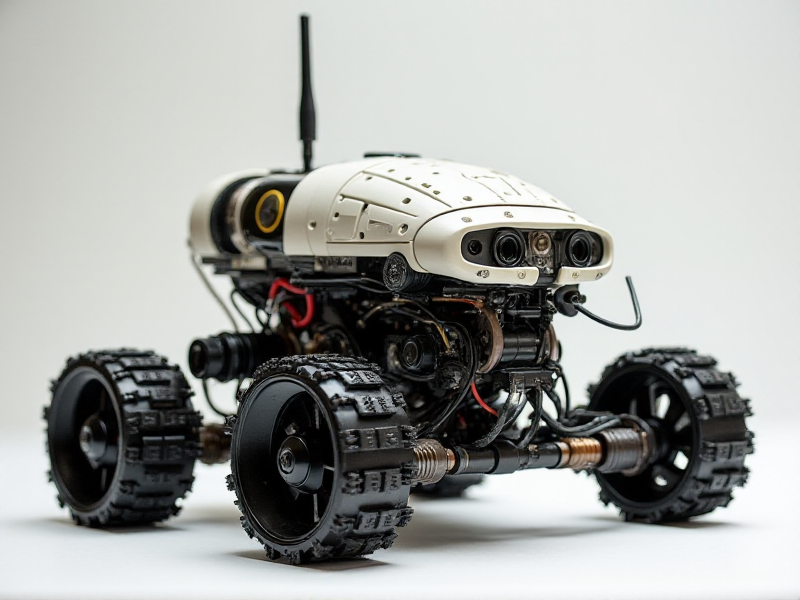
ai-renders/all/00265-995517853.png
