positron48/robot/ai-renders/all/00270-389780353.png

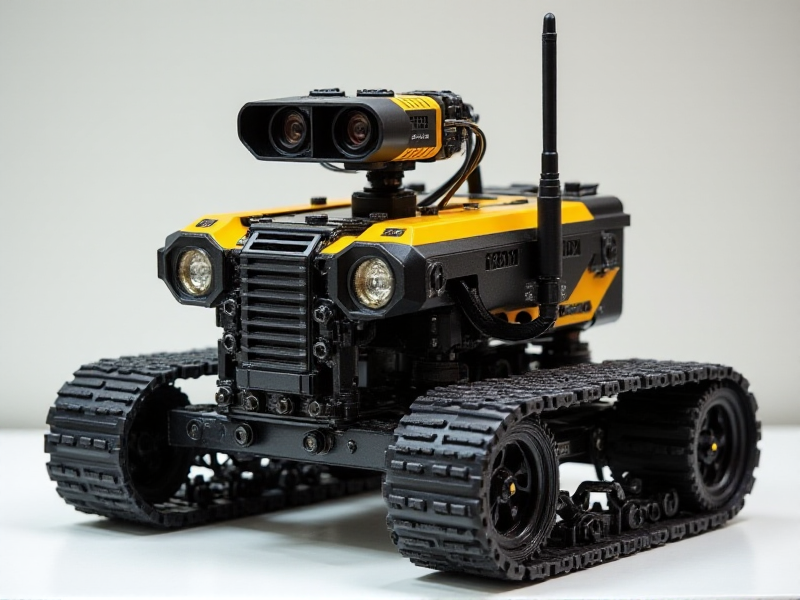
ai-renders/all/00270-389780353.png
