positron48/robot/ai-renders/all/00275-1887556602.png

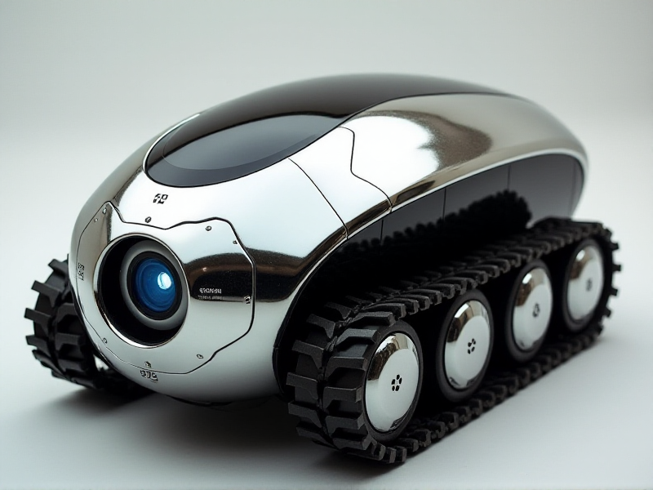
ai-renders/all/00275-1887556602.png
