positron48/robot/ai-renders/all/00280-1424854579.png

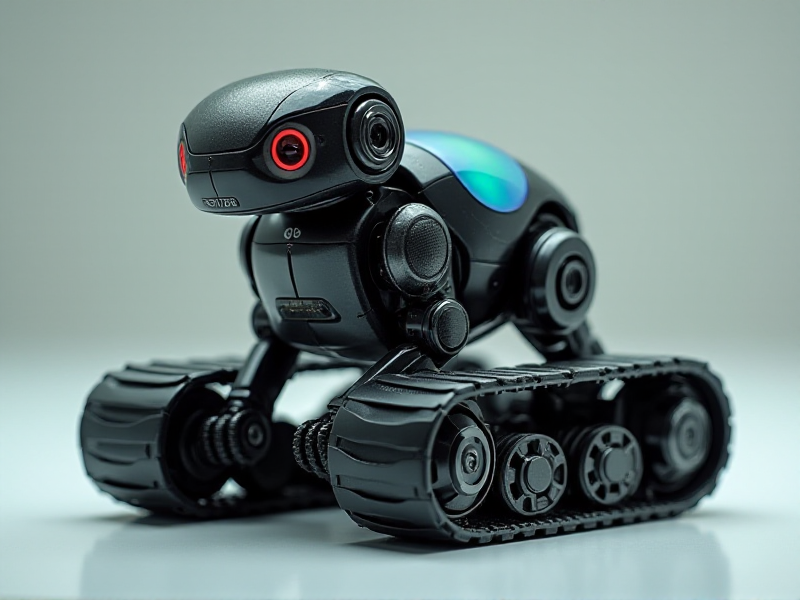
ai-renders/all/00280-1424854579.png
