positron48/robot/ai-renders/all/00285-435748618.png

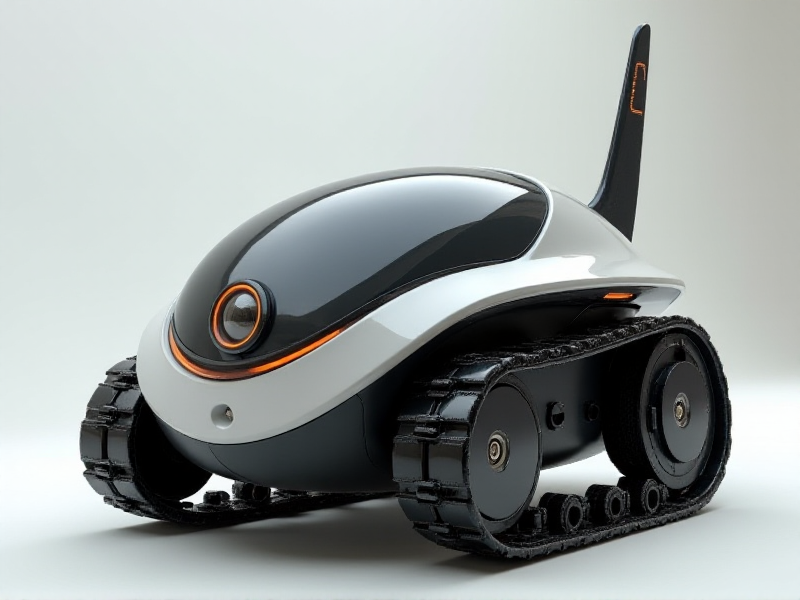
ai-renders/all/00285-435748618.png
