positron48/robot/ai-renders/all/00290-3687651719.png

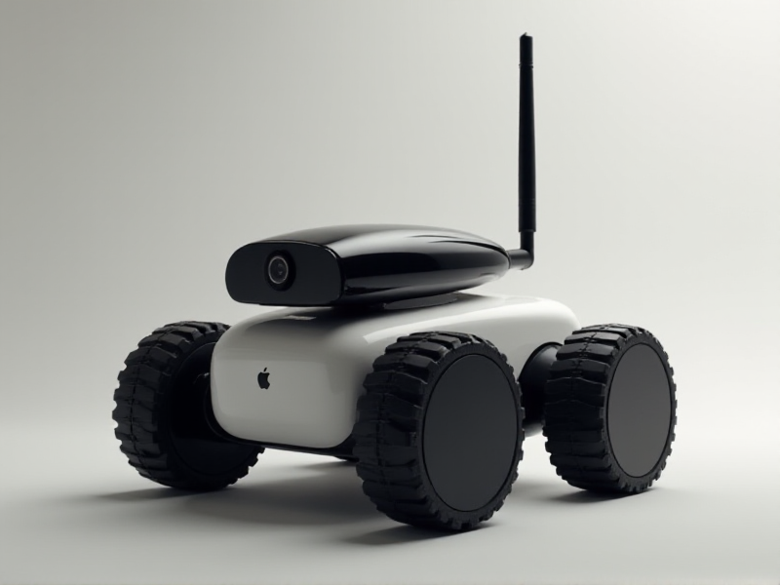
ai-renders/all/00290-3687651719.png
