positron48/robot/ai-renders/all/00295-4196220442.png

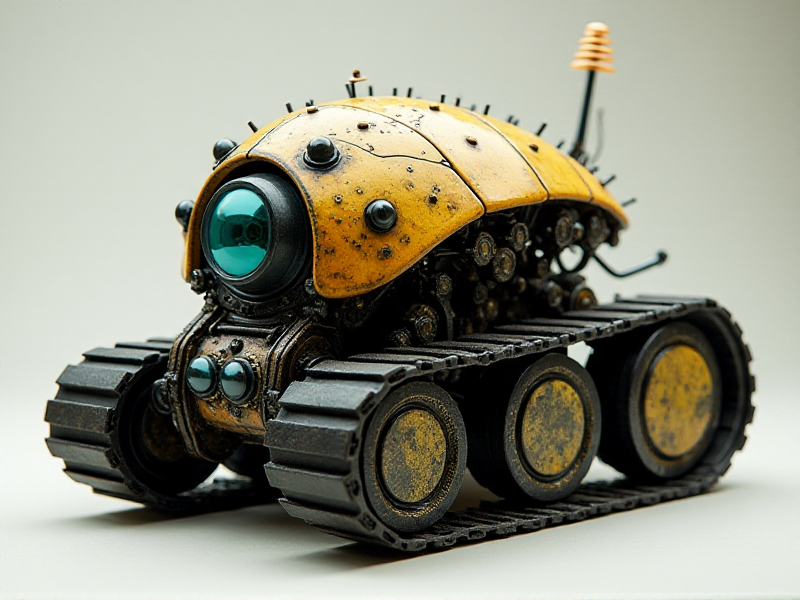
ai-renders/all/00295-4196220442.png
