positron48/robot/ai-renders/all/00300-2526889251.png

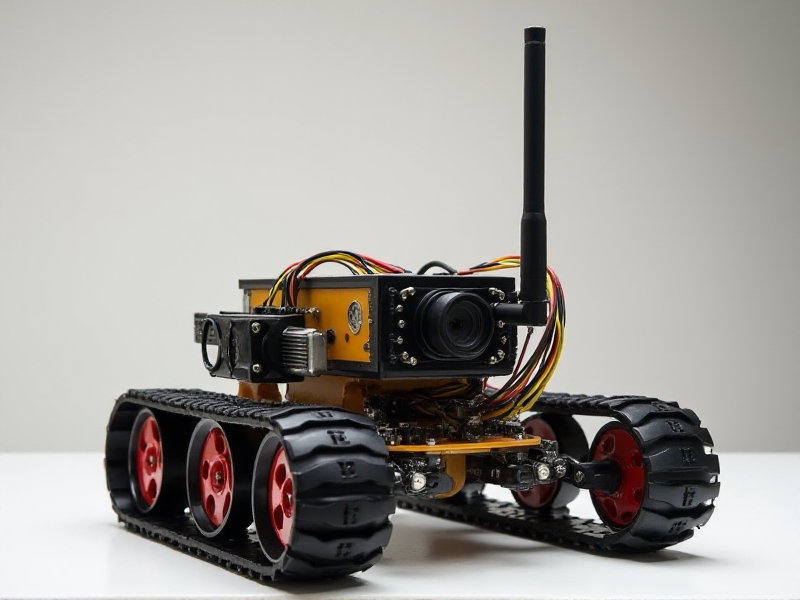
ai-renders/all/00300-2526889251.png
