positron48/robot/ai-renders/all/00305-3705304558.png

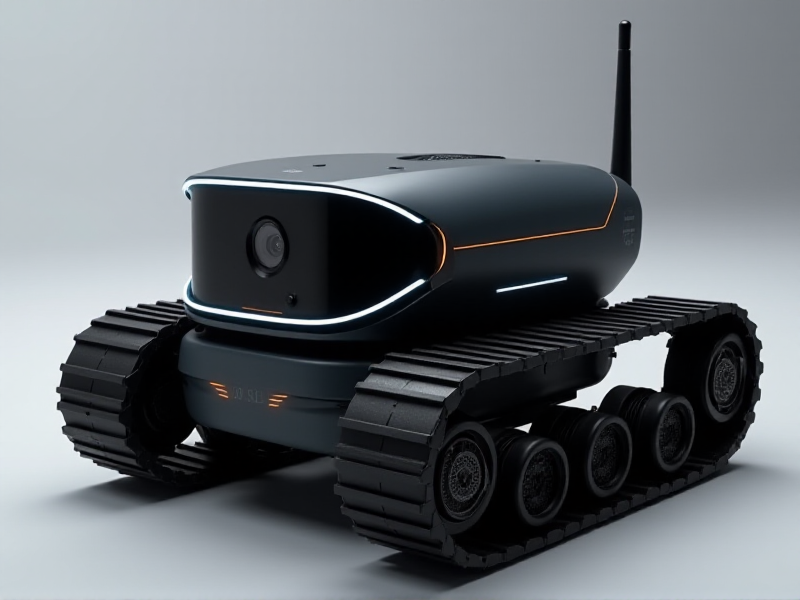
ai-renders/all/00305-3705304558.png
