positron48/robot/ai-renders/all/00310-3693409764.png

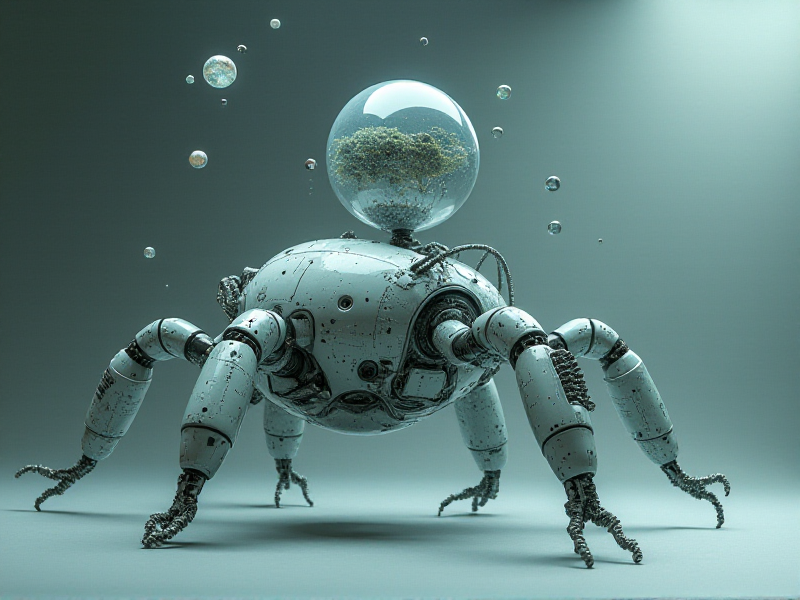
ai-renders/all/00310-3693409764.png
