positron48/robot/ai-renders/all/00315-3680724376.png

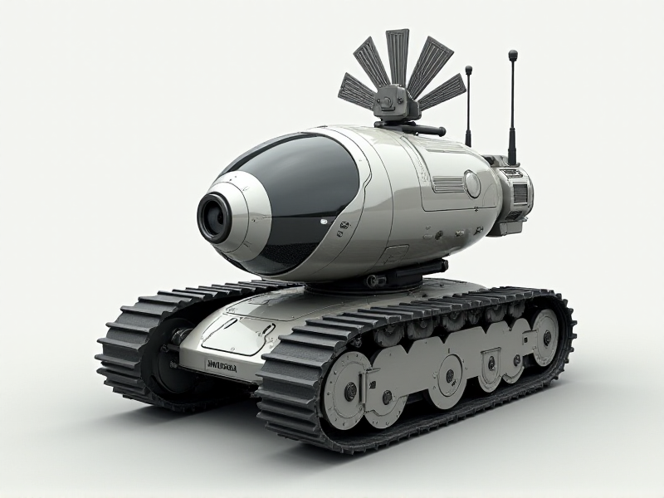
ai-renders/all/00315-3680724376.png
