positron48/robot/ai-renders/all/00320-3574186289.png

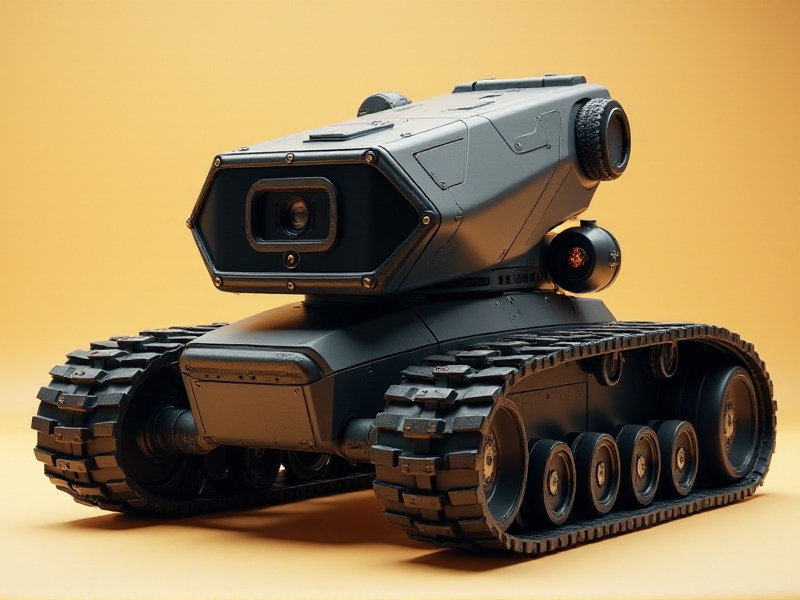
ai-renders/all/00320-3574186289.png
