positron48/robot/ai-renders/all/00330-688510005.png

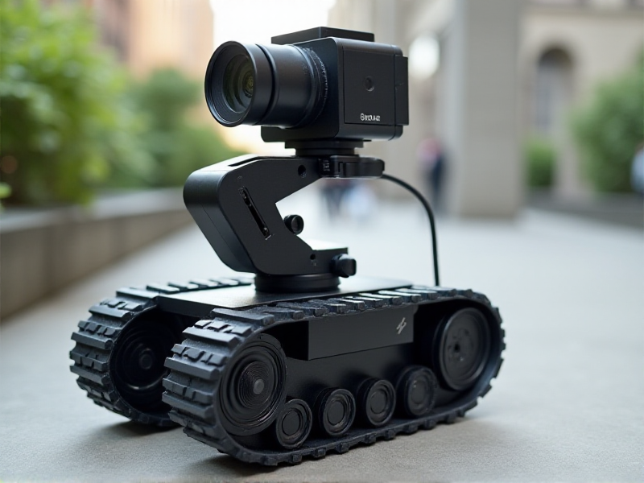
ai-renders/all/00330-688510005.png
