positron48/robot/ai-renders/all/00335-1095681119.png

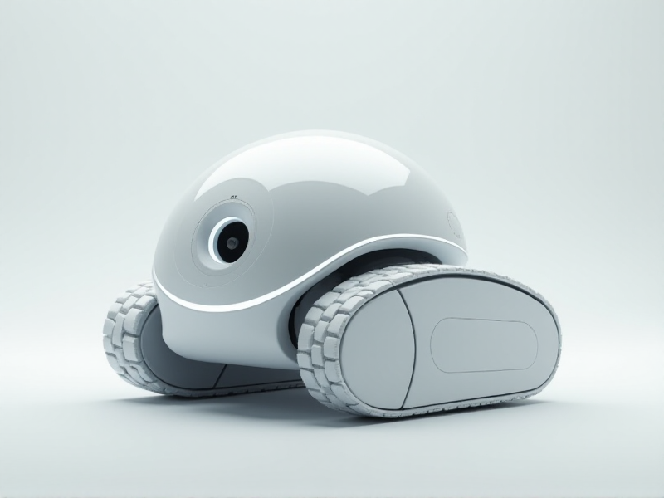
ai-renders/all/00335-1095681119.png
