positron48/robot/ai-renders/all/00345-3517302315.png

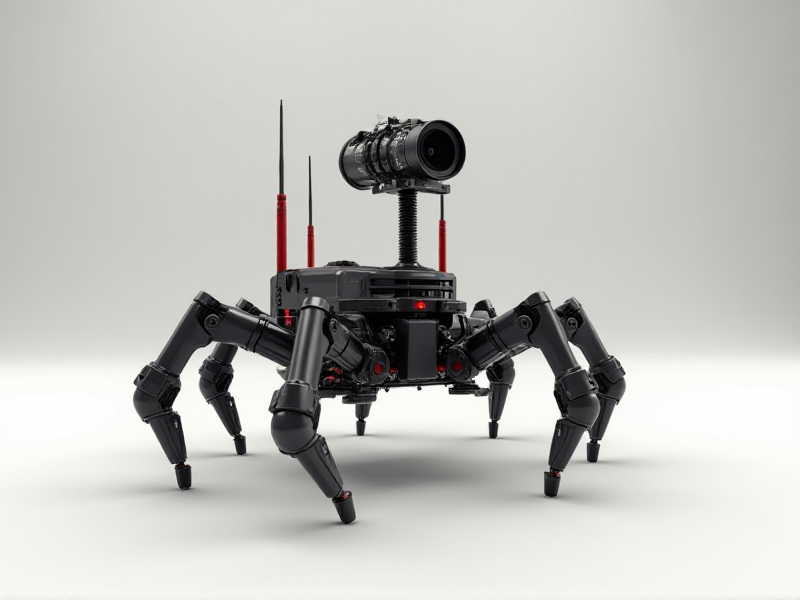
ai-renders/all/00345-3517302315.png
