positron48/robot/ai-renders/all/00350-2386233243.png

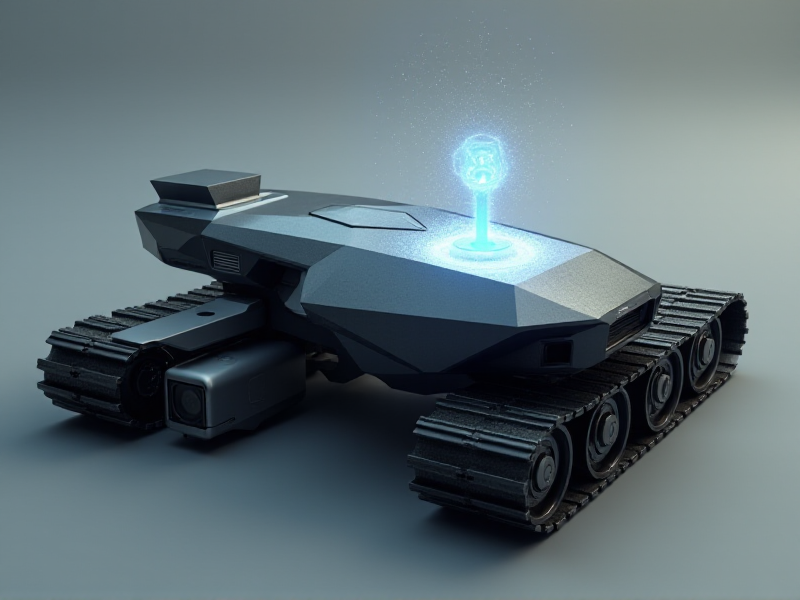
ai-renders/all/00350-2386233243.png
