positron48/robot/ai-renders/all/00360-939549896.png

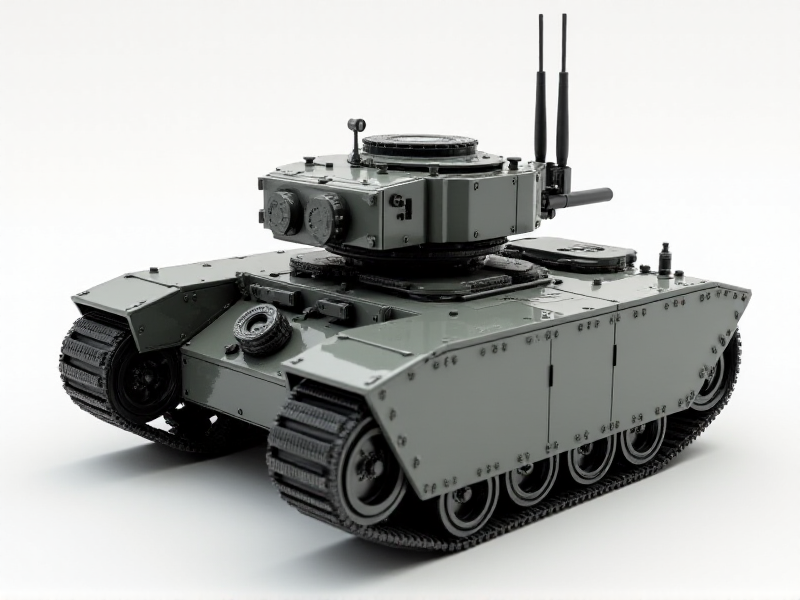
ai-renders/all/00360-939549896.png
