positron48/robot/ai-renders/all/00365-4077331270.png

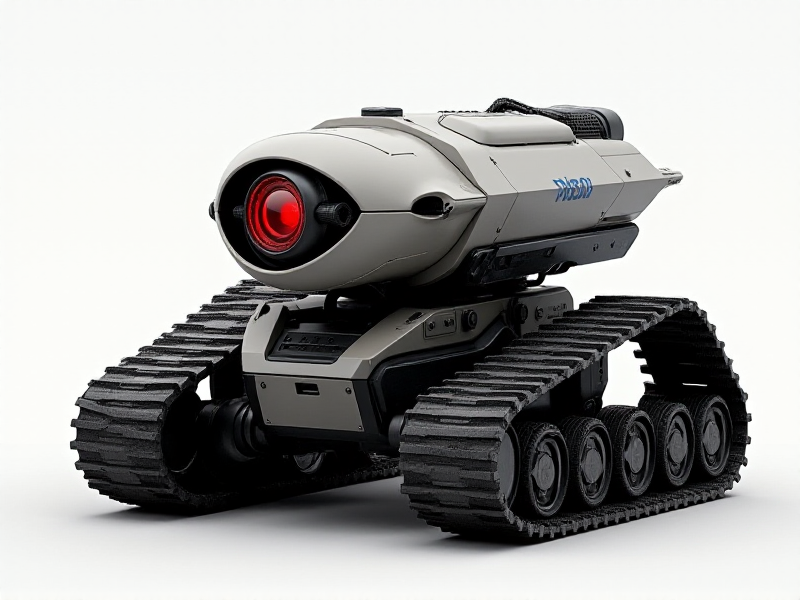
ai-renders/all/00365-4077331270.png
