positron48/robot/ai-renders/all/00375-3405695622.png

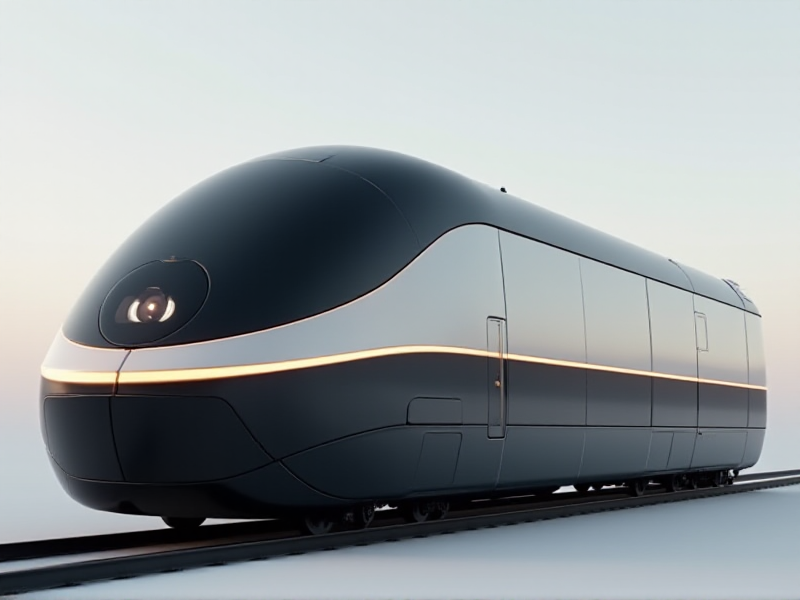
ai-renders/all/00375-3405695622.png
