positron48/robot/ai-renders/all/00380-2456719310.png

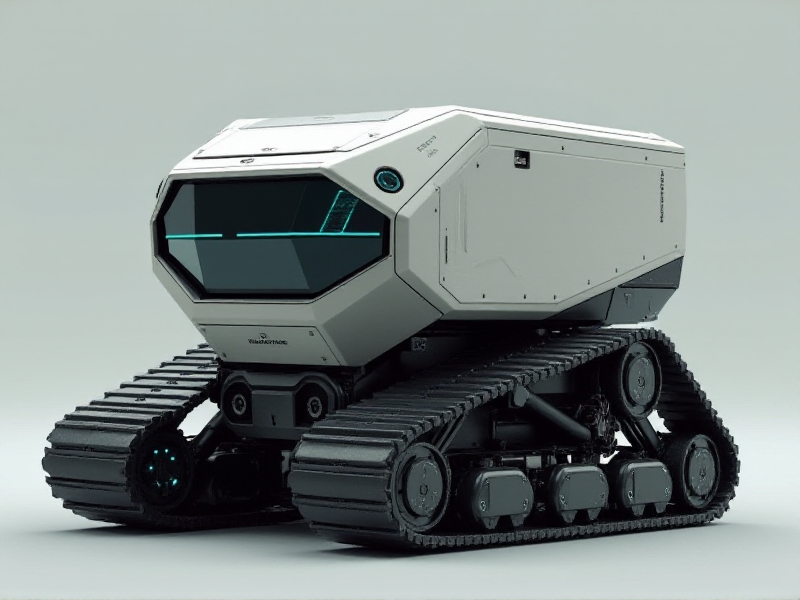
ai-renders/all/00380-2456719310.png
