positron48/robot/ai-renders/all/00390-2234824293.png

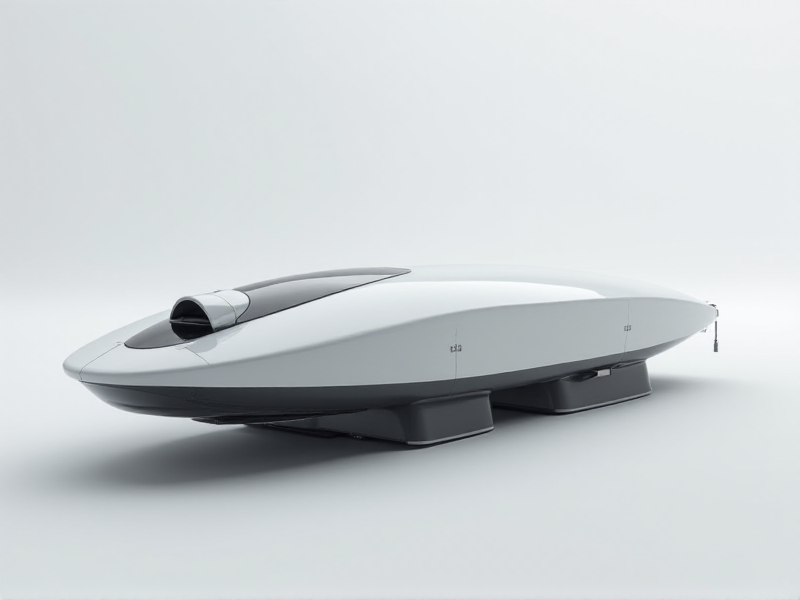
ai-renders/all/00390-2234824293.png
