positron48/robot/ai-renders/all/00395-2466875607.png

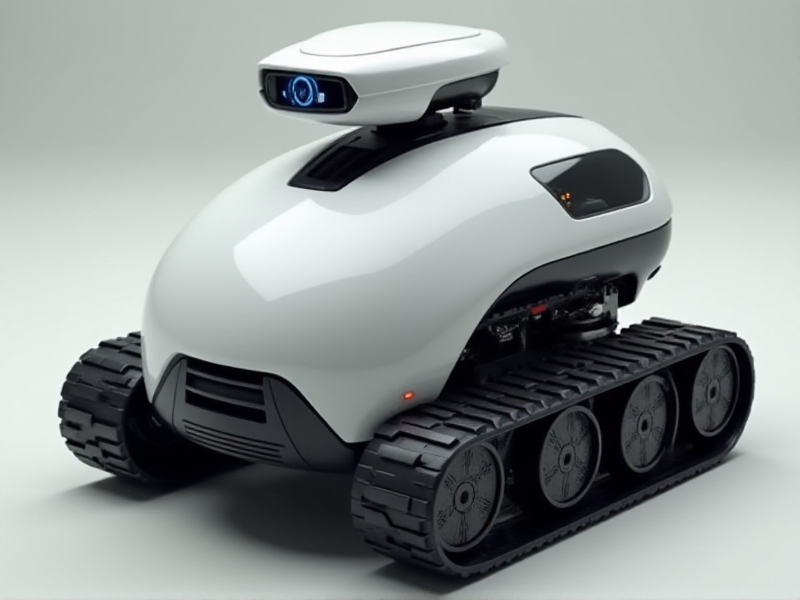
ai-renders/all/00395-2466875607.png
