positron48/robot/ai-renders/all/00405-2380778064.png

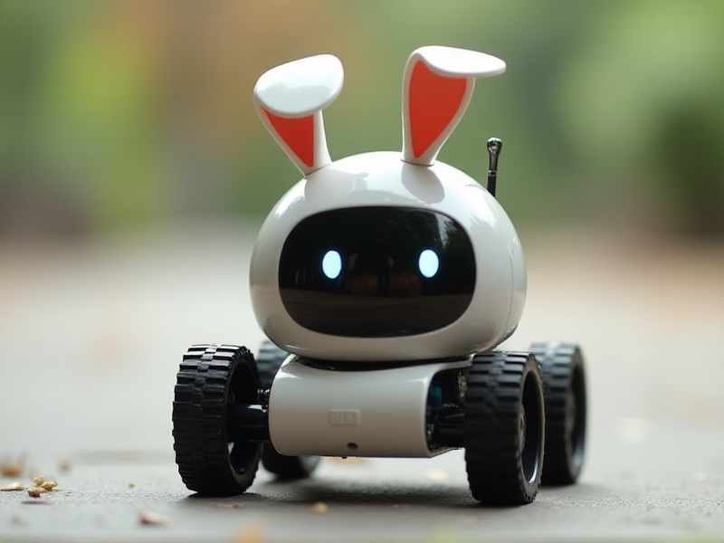
ai-renders/all/00405-2380778064.png
