positron48/robot/ai-renders/all/00410-624065046.png

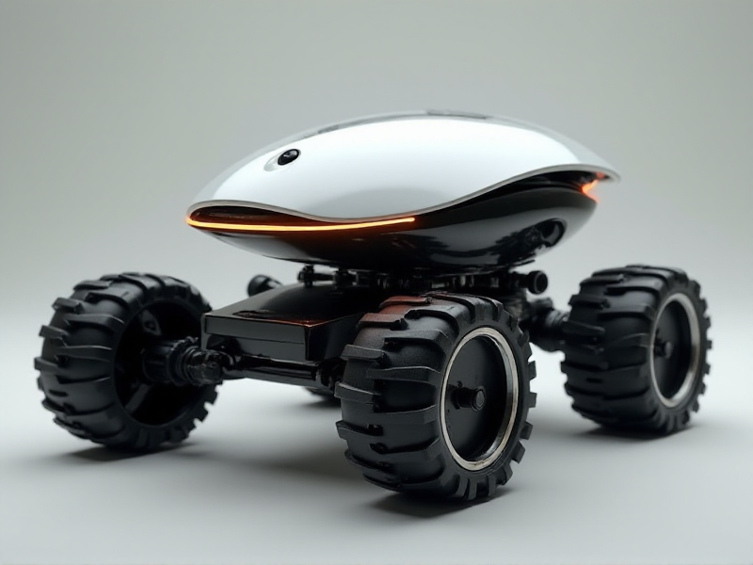
ai-renders/all/00410-624065046.png
