positron48/robot/ai-renders/all/00420-3753778383.png

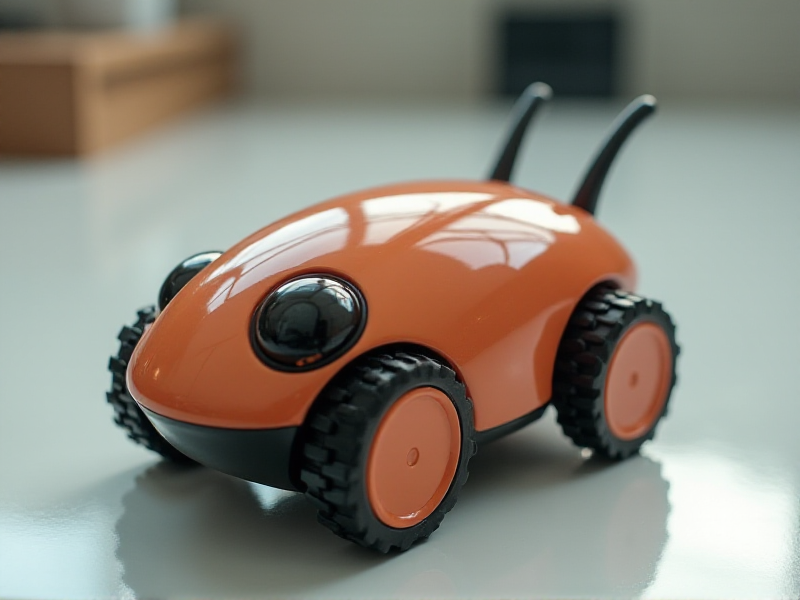
ai-renders/all/00420-3753778383.png
