positron48/robot/ai-renders/all/00435-1029277670.png

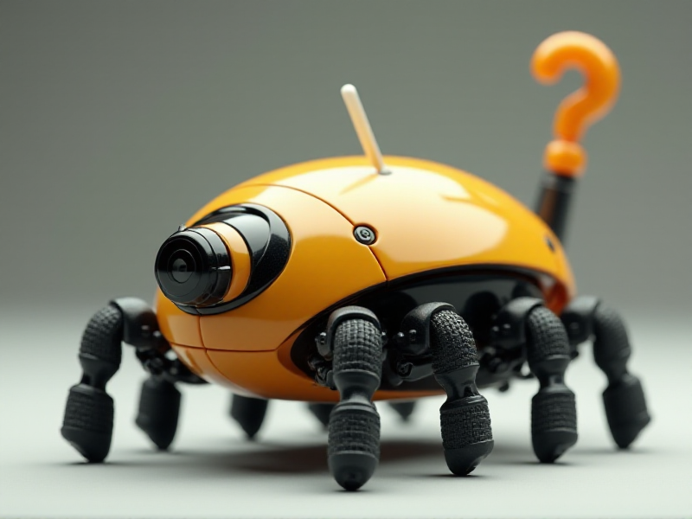
ai-renders/all/00435-1029277670.png
