positron48/robot/ai-renders/all/00450-3858477374.png

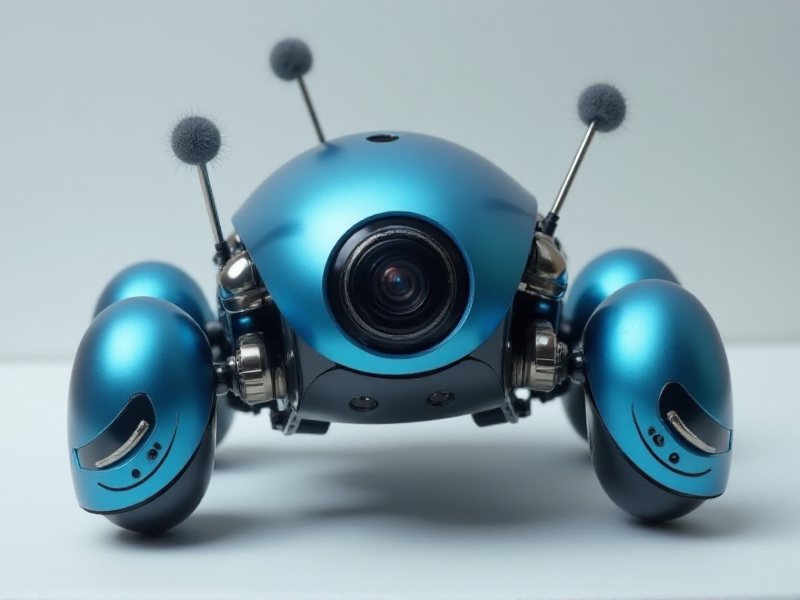
ai-renders/all/00450-3858477374.png
