positron48/robot/ai-renders/all/00465-2991570850.png

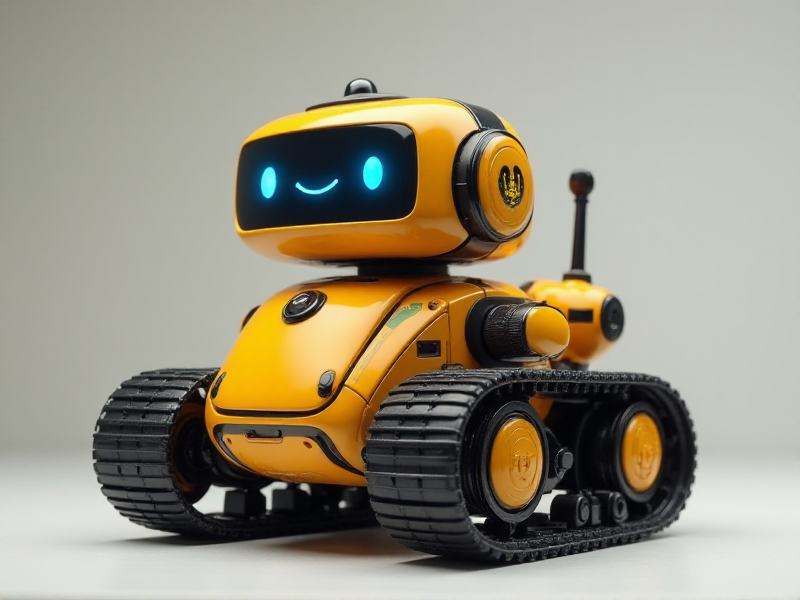
ai-renders/all/00465-2991570850.png
