positron48/robot/ai-renders/all/00480-786677740.png

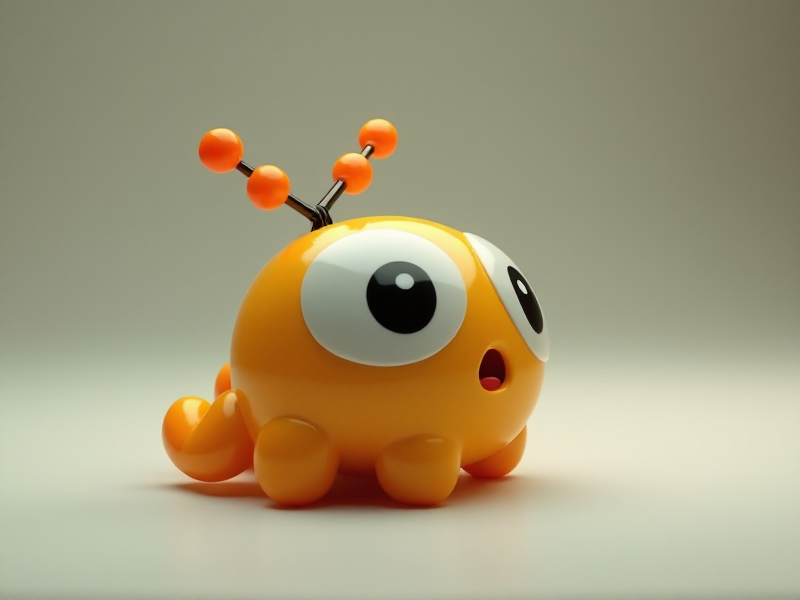
ai-renders/all/00480-786677740.png
