positron48/robot/ai-renders/all/00495-2324976370.png

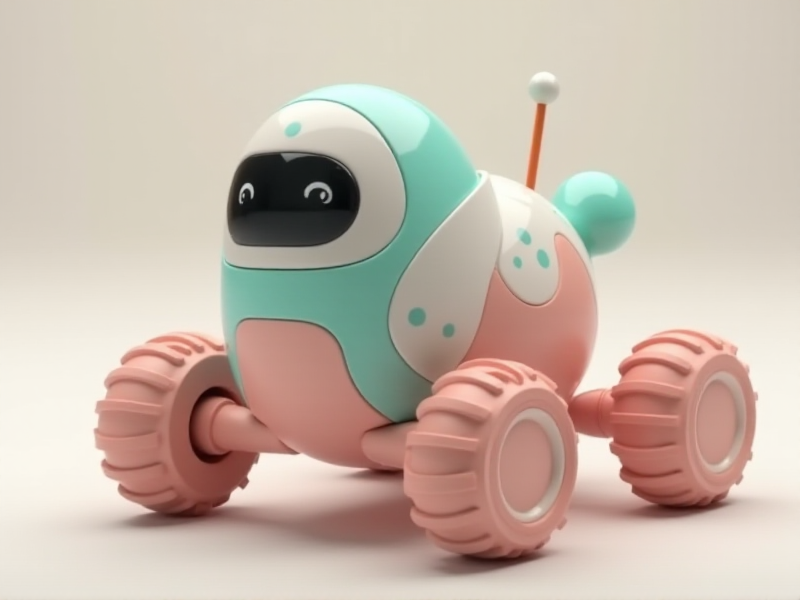
ai-renders/all/00495-2324976370.png
