positron48/robot/ai-renders/all/00510-2652253227.png

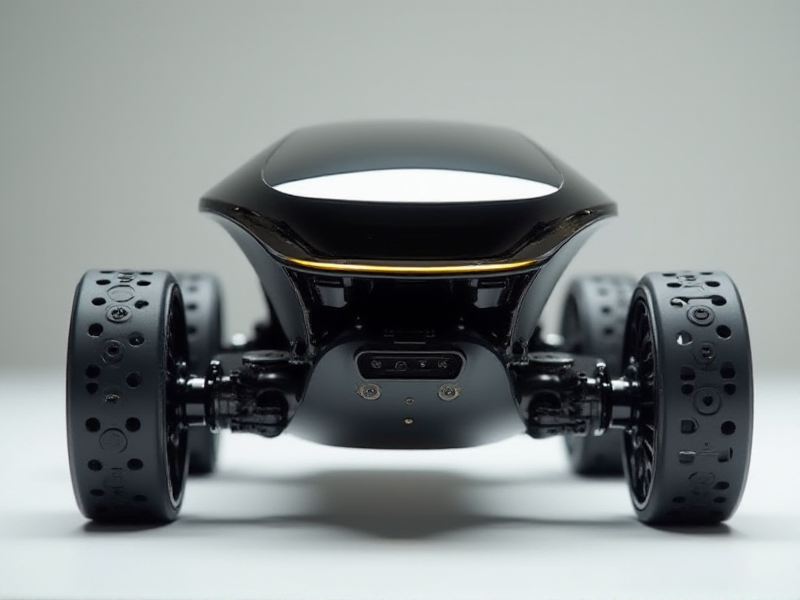
ai-renders/all/00510-2652253227.png
