positron48/robot/ai-renders/all/00525-1785617539.png

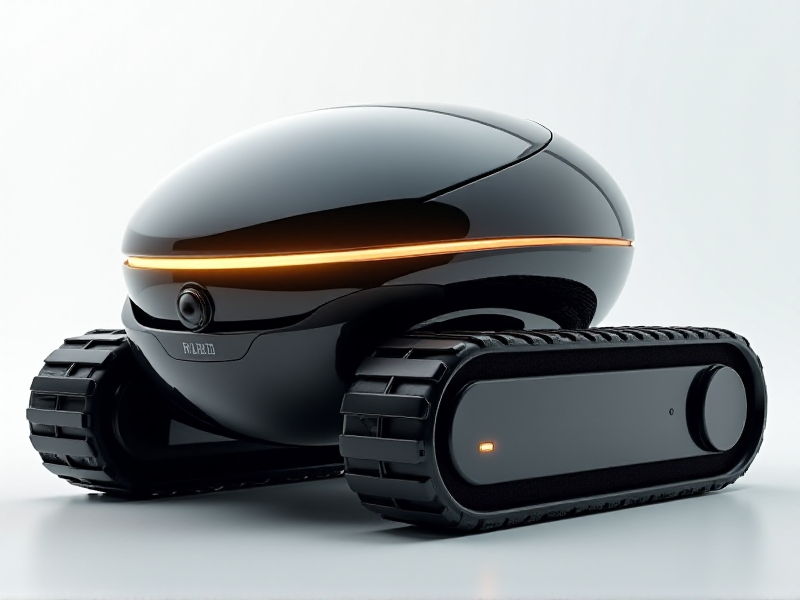
ai-renders/all/00525-1785617539.png
