positron48/robot/ai-renders/all/00540-2961557581.png

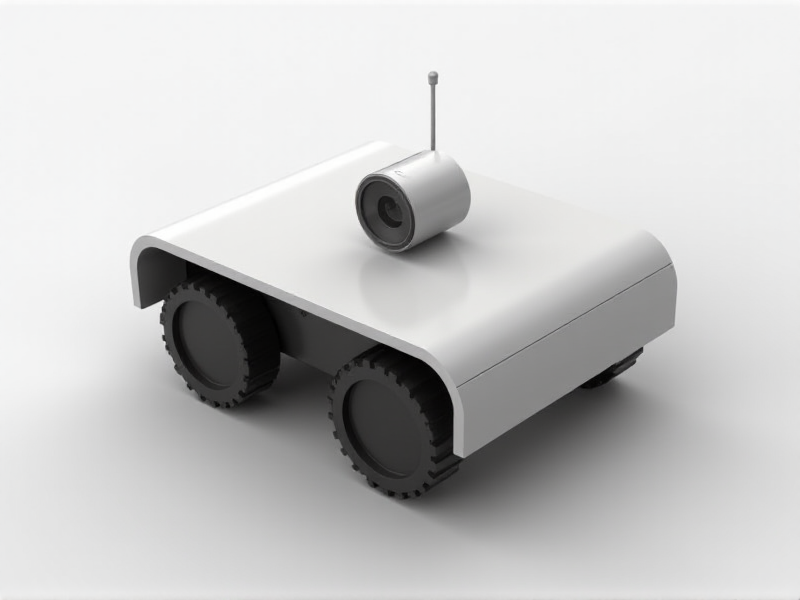
ai-renders/all/00540-2961557581.png
