positron48/robot/ai-renders/all/00555-645231692.png

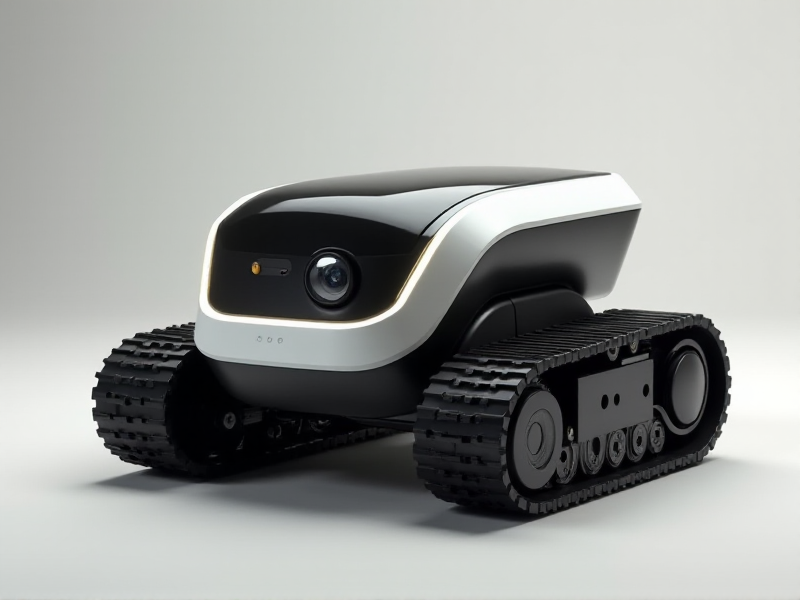
ai-renders/all/00555-645231692.png
