positron48/robot/ai-renders/all/00570-1258968112.png

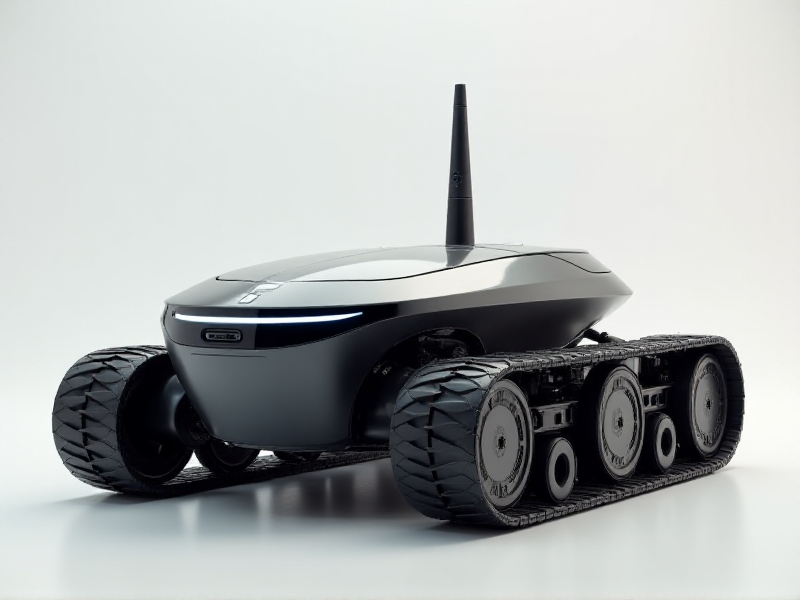
ai-renders/all/00570-1258968112.png
