positron48/robot/ai-renders/all/00585-2851518708.png

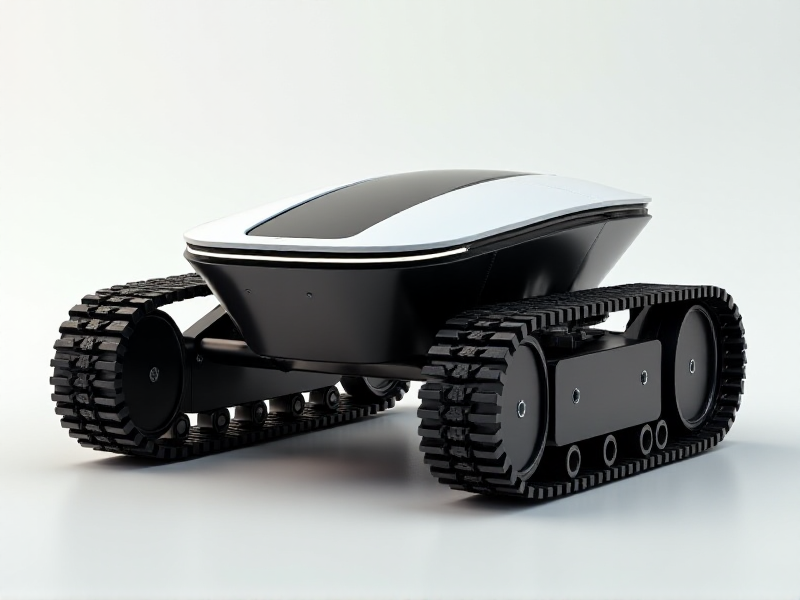
ai-renders/all/00585-2851518708.png
