positron48/robot/ai-renders/all/00600-3488248658.png

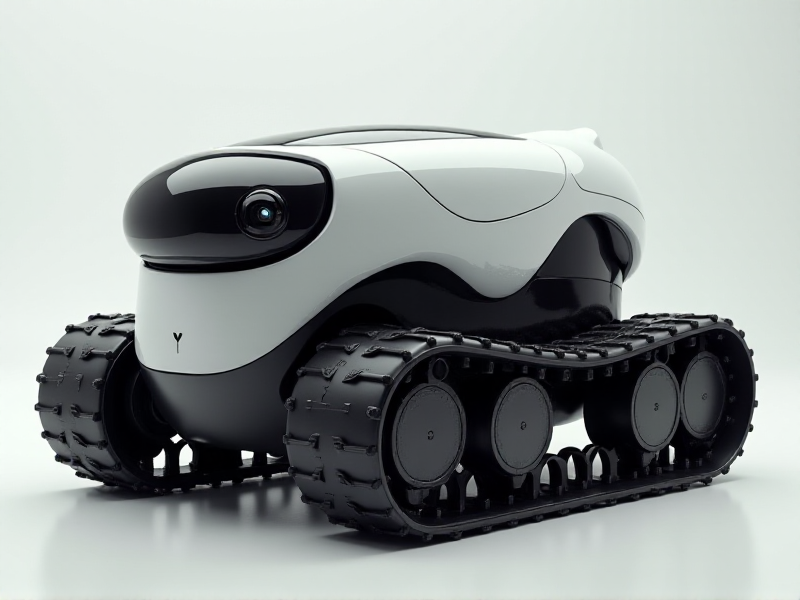
ai-renders/all/00600-3488248658.png
