positron48/robot/ai-renders/all/00615-1688247058.png

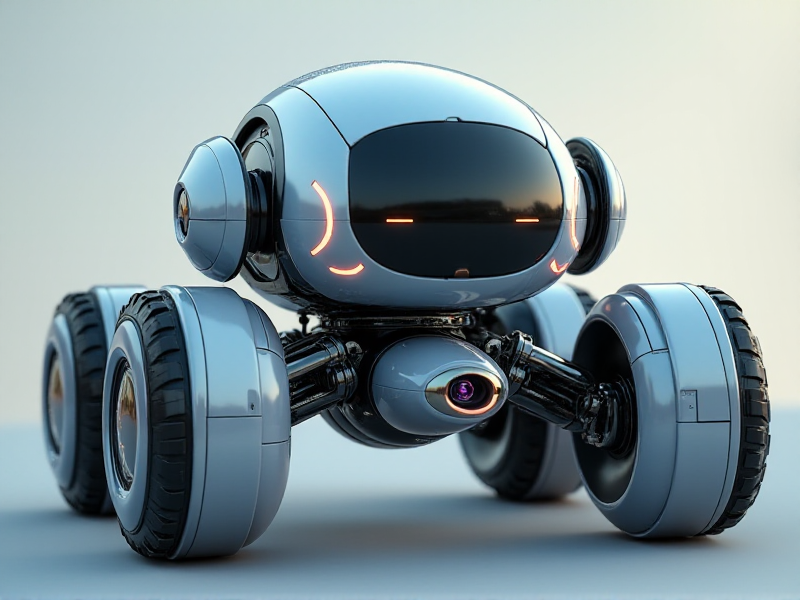
ai-renders/all/00615-1688247058.png
