positron48/robot/ai-renders/all/00630-2904871216.png

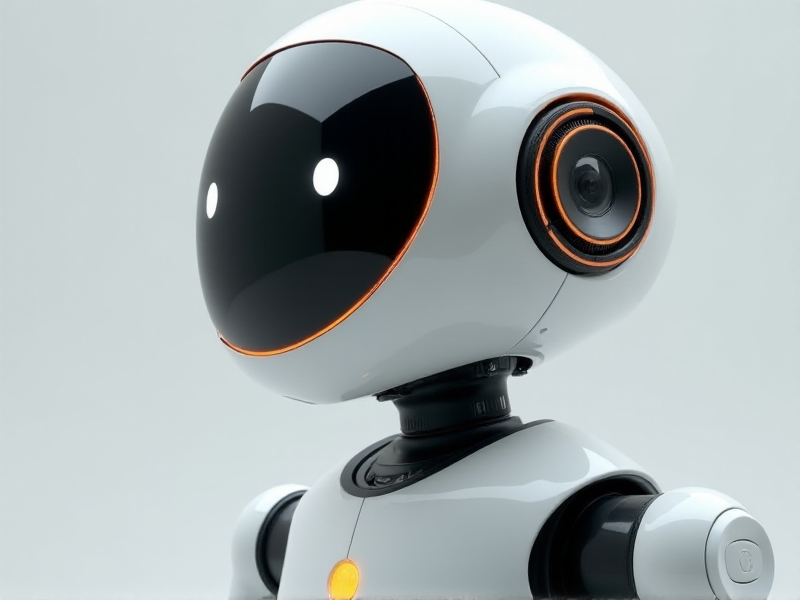
ai-renders/all/00630-2904871216.png
