positron48/robot/ai-renders/all/00645-1894595010.png

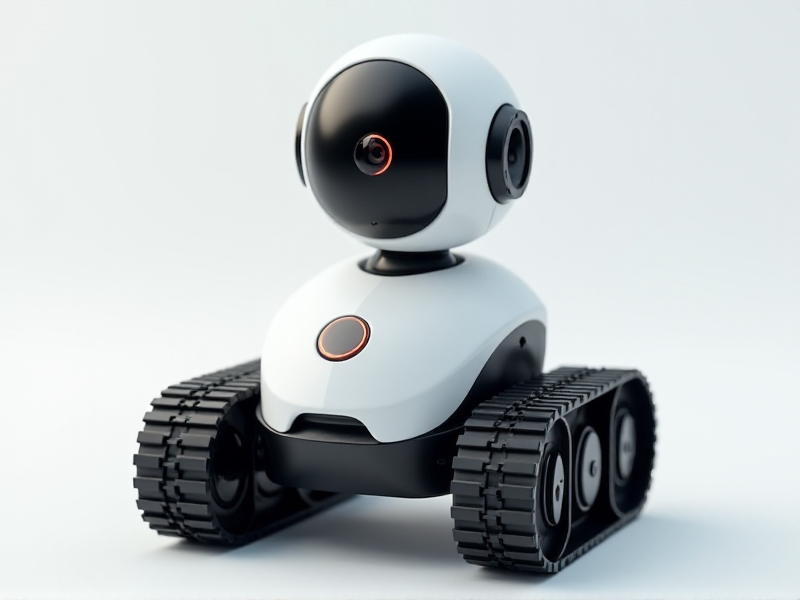
ai-renders/all/00645-1894595010.png
