positron48/robot/ai-renders/all/00660-1642268829.png

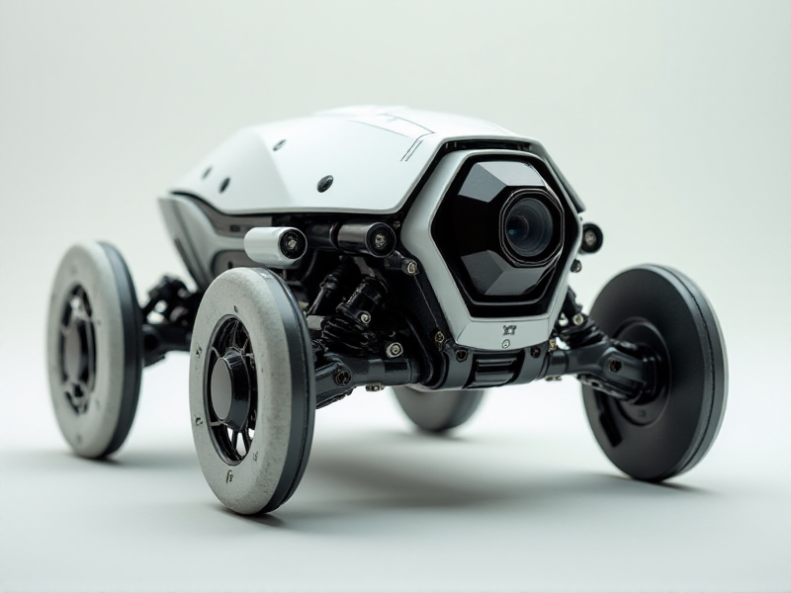
ai-renders/all/00660-1642268829.png
