positron48/robot/ai-renders/all/00675-1969294178.png

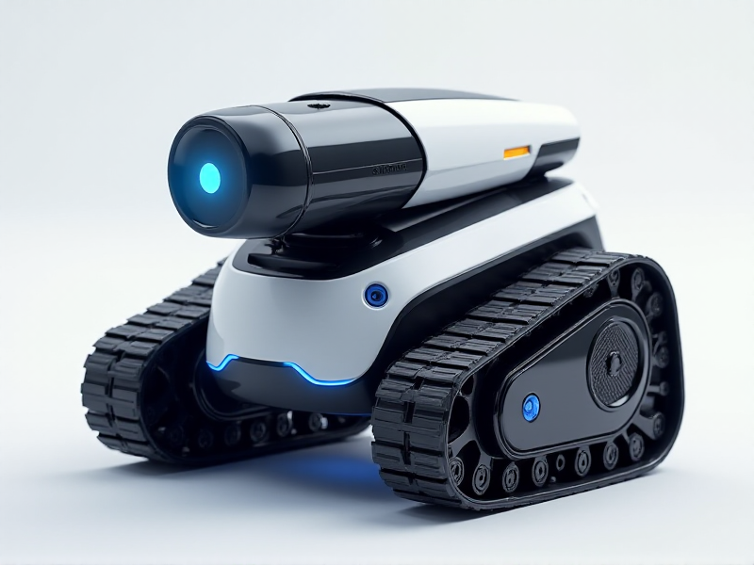
ai-renders/all/00675-1969294178.png
