positron48/robot/ai-renders/output_collage.jpg

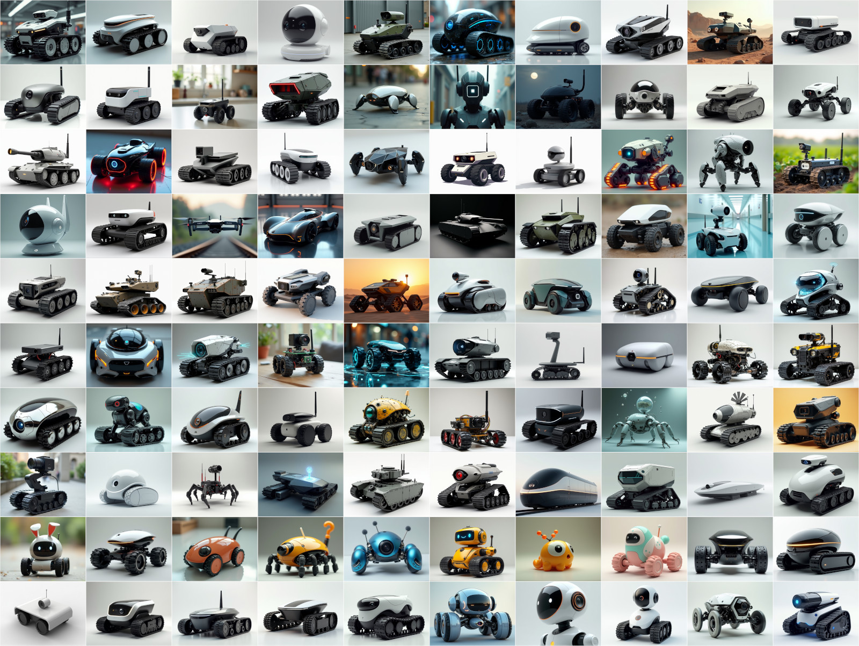
ai-renders/output_collage.jpg
