positron48/robot/models/caretaker-top.stl

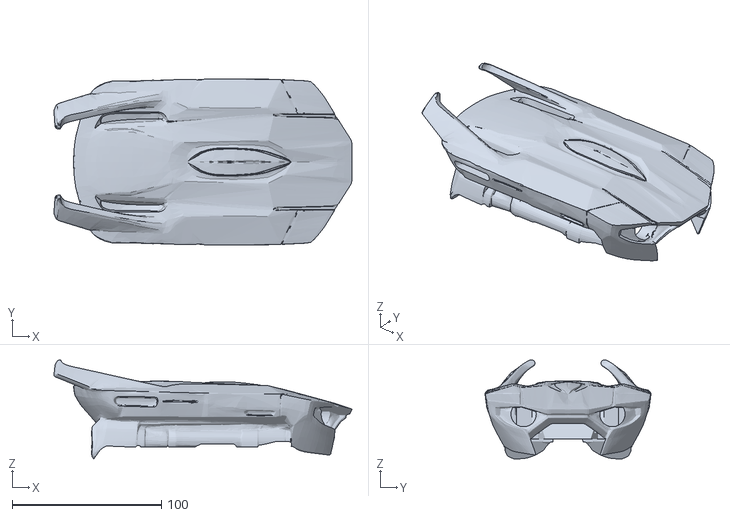
[picture p137: CAD file, 2025-04-07]
models/caretaker-top.stl
199.7 x 111.5 x 66.3
