positron48/robot/models/eye-inner (x2 mirrored).step

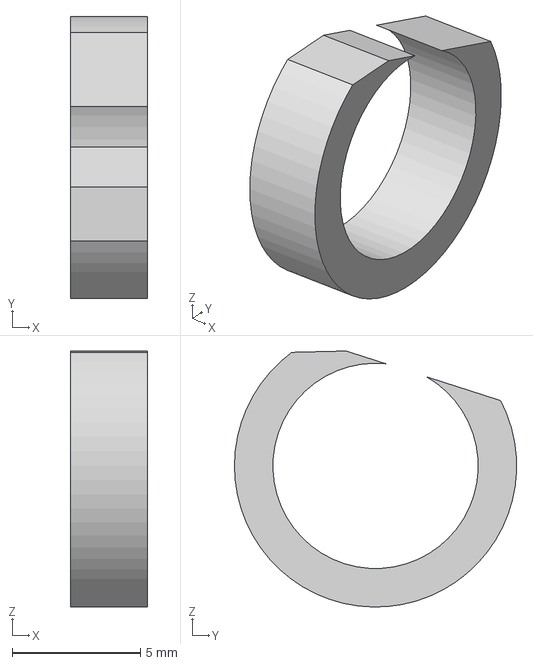
[picture p138: CAD file, 2025-04-07]
models/eye-inner (x2 mirrored).step
3.00 x 11.0 x 9.98 mm
