positron48/robot/models/base-platform.step

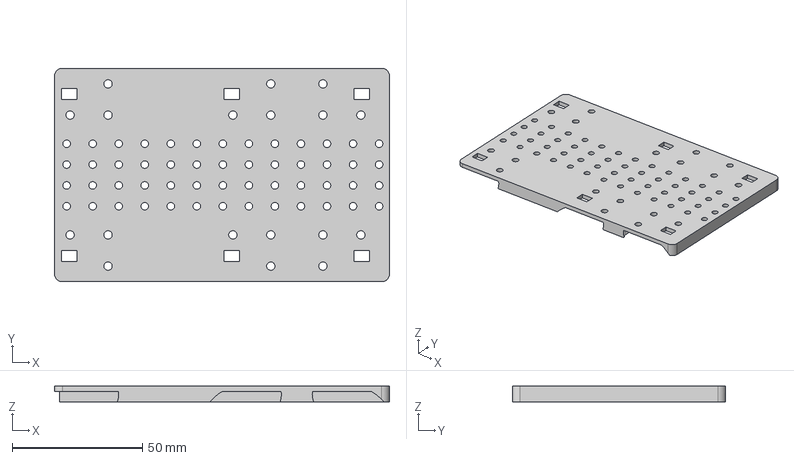
[picture p139: CAD file, 2025-04-07]
models/base-platform.step
128.7 x 82.0 x 6.00 mm
