positron48/robot/models/wheel-inner (x6).step

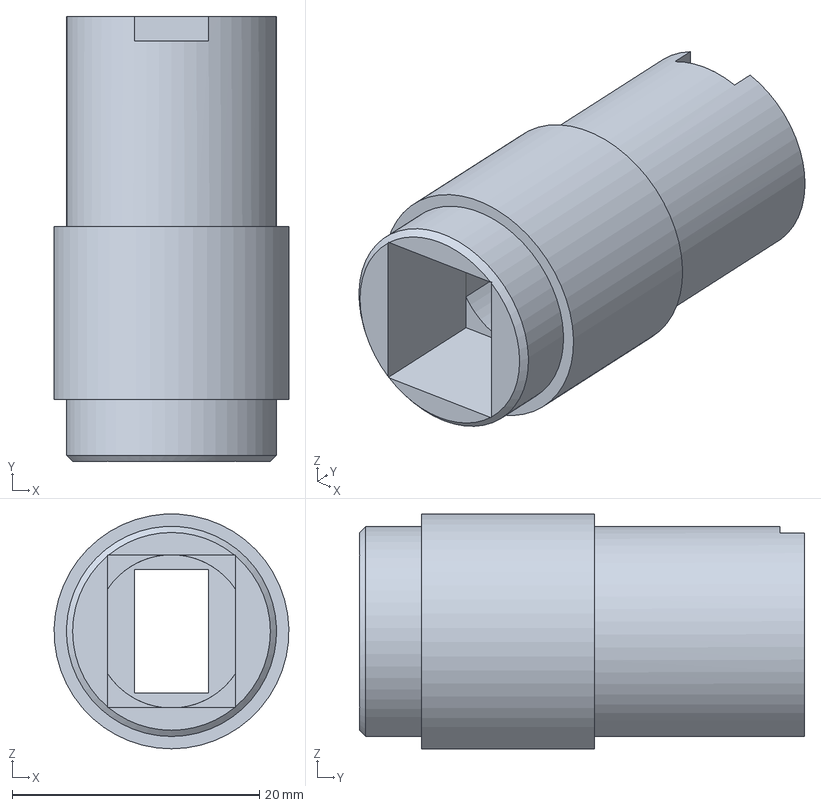
[picture p140: CAD file, 2025-04-07]
models/wheel-inner (x6).step
19.0 x 36.0 x 19.0 mm
