positron48/robot/board/caretaker.kicad_sch

## KiCad design board/caretaker.kicad_sch (2025-04-07)

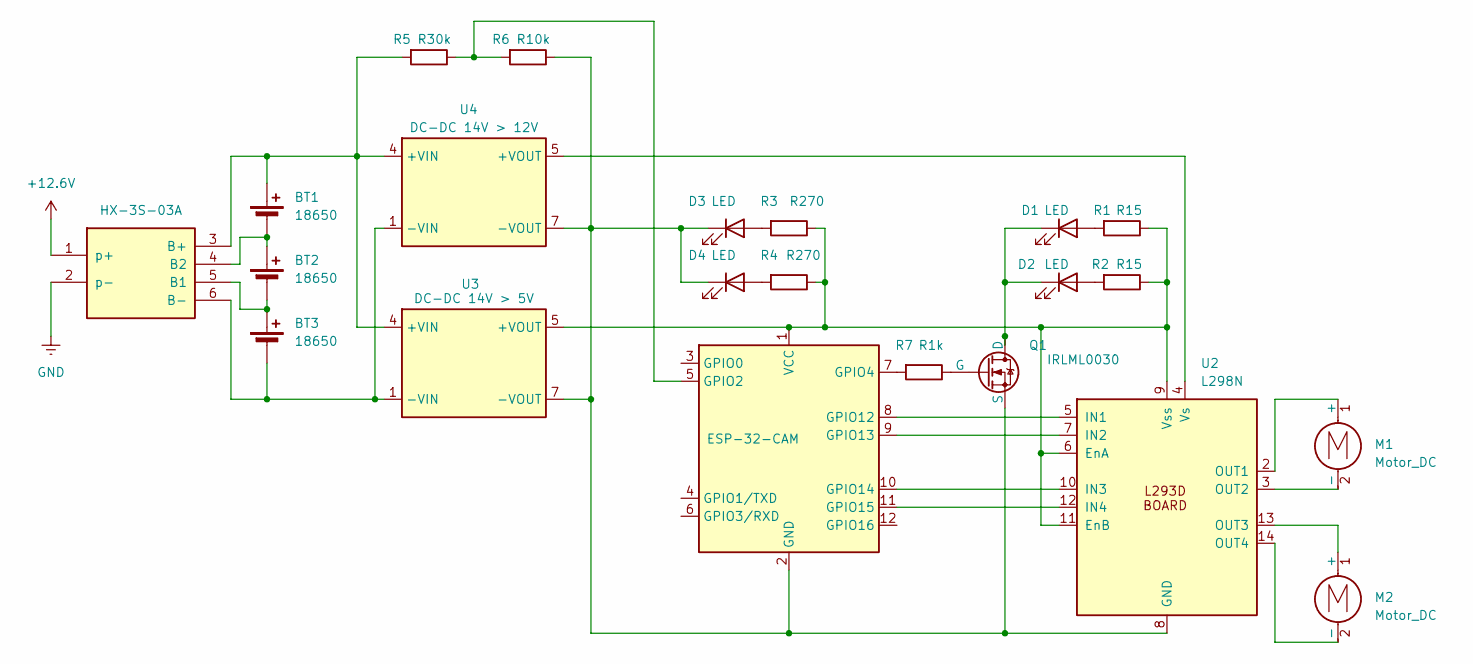
[picture p141: schematic caretaker.kicad_sch]

Parts:
BT1, BT2, BT3: 18650
D1, D2, D3, D4: LED
HX-3S-03: BMS_3S_[custom]
M1, M2: Motor_DC
Q1: IRLML0030
R1, R2: R15
R3, R4: R270
R5: R30k
R6: R10k
R7: R1k
U1: ESP-32-CAM; ESP-07
U2: L298N; TO-220-15_P2.54x2.54mm_StaggerOdd_Lead4.58mm_Vertical
U3: DC-DC 14V > 5V
U4: DC-DC 14V > 12V

Connections:
+12.6V: HX-3S-03.1 (p+)
GND: HX-3S-03.2 (p-)
unnamed: BT1.1 (+), HX-3S-03.3 (B+), R5.2, U3.4 (+VIN), U4.4 (+VIN)
unnamed: BT1.2 (-), BT2.1 (+), HX-3S-03.4 (B2)
unnamed: BT2.2 (-), BT3.1 (+), HX-3S-03.5 (B1)
unnamed: BT3.2 (-), HX-3S-03.6 (B-), U3.1 (-VIN), U4.1 (-VIN)
unnamed: D1.1 (K), D2.1 (K), Q1.1 (D)
unnamed: D1.2 (A), R1.2
unnamed: D2.2 (A), R2.2
unnamed: D3.1 (K), D4.1 (K), Q1.3 (S), R6.1, U1.2 (GND), U2.8 (GND), U3.7 (-VOUT), U4.7 (-VOUT)
unnamed: D3.2 (A), R3.2
unnamed: D4.2 (A), R4.2
unnamed: M1.1 (+), U2.2 (OUT1)
unnamed: M1.2 (-), U2.3 (OUT2)
unnamed: M2.1 (+), U2.13 (OUT3)
unnamed: M2.2 (-), U2.14 (OUT4)
unnamed: Q1.2 (G), R7.1
unnamed: R1.1, R2.1, R3.1, R4.1, U1.1 (VCC), U2.6 (EnA), U2.9 (Vss), U2.11 (EnB), U3.5 (+VOUT)
unnamed: R5.1, R6.2, U1.5 (GPIO2)
unnamed: R7.2, U1.7 (GPIO4)
unnamed: U1.8 (GPIO12), U2.5 (IN1)
unnamed: U1.9 (GPIO13), U2.7 (IN2)
unnamed: U1.10 (GPIO14), U2.10 (IN3)
unnamed: U1.11 (GPIO15), U2.12 (IN4)
unnamed: U2.4 (Vs), U4.5 (+VOUT)
